ErickHuancas/FdD_Equipo_03/Proyecto/Módulo Mecánico/V3.0/Bocetos/Estructura interna frontal V.3.0.pdf

Título del Proyecto: | Estructura interna frontal del dispositivo

Dibujado por:

Paloma Fernanda
Velasquez Saforas

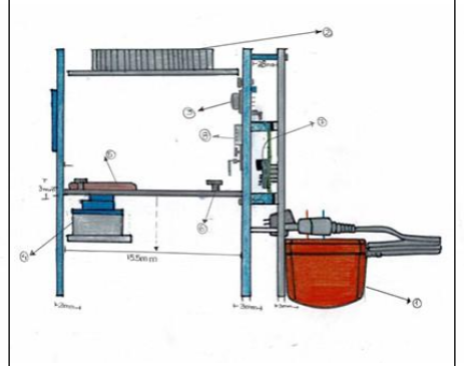
[picture p7: figure]

Descripción del funcionamiento | Lista de Despiece
La vista interna frontal del dispositivo muestra la distribución de los componentes encargados de la captura y procesamiento de datos. En la parte superior se encuentran el módulo ESP32-CAM, la luz LED, el sensor de gas MQ135 y el sensor de temperatura y humedad DHT22, que permiten la adquisición de imágenes y el monitoreo de las condiciones ambientales. En la zona central se ubica | Pieza | Nombre
| 1 | Cargador
| 2 | Luz led
| 3 | Sensor de gas (MQ135)
| 4 | Servomotor
| 5 | Base de soporte del tomate
| 6 | Tornillo

la base de soporte del tomate, acoplada a un servomotor que facilita su rotación para la captura de imágenes desde diferentes ángulos. Finalmente, el sistema es alimentado mediante un cargador y los componentes se encuentran fijados mediante

7 | Módulo ESP32-CAM

t

o

rn

i

l

l

o

s. 8

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
