ErickHuancas/FdD_Equipo_03/Proyecto/Módulo Mecánico/V3.0/Bocetos/Estructura interna V.3.0.pdf

Título del Proyecto: | Estructura externa del dispositivo

Dibujado por:

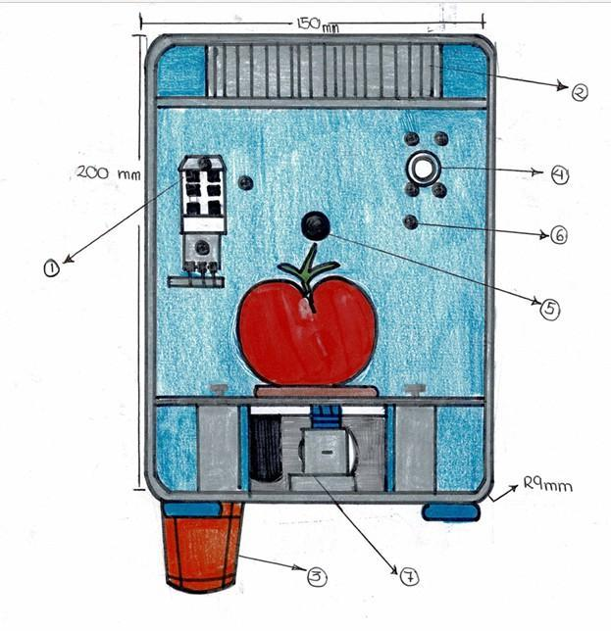
[picture p8: figure]

Paloma Fernanda
Velasquez Saforas
Descripción del funcionamiento | Lista de Despiece
| Pieza | Nombre
| 1 | Sensor de temperatura y humedad (DHT22)
| 2 | Luz led
| 3 | Cargador
| 4 | Sensor de gas (MQ135)
| 5 | Cámara
| 6 | Tornillo

7 | Servomotor
