ErickHuancas/FdD_Equipo_03/Proyecto/Módulo Mecánico/V3.0/Bocetos/Parte trasera V.3.0.pdf

Título del Proyecto: | Parte trasera del dispositivo

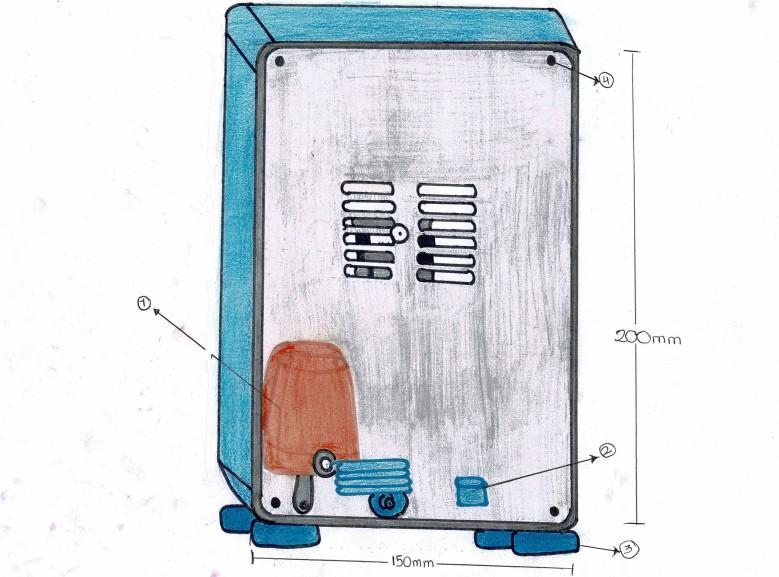
[picture p9: figure]

Dibujado por:

Paloma Fernanda
Velasquez Saforas
Descripción del funcionamiento | Lista de Despiece
| Pieza | Nombre
| 1 | El cargador
| 2 | Interruptor de encendido y apagado
| 3 | soportes
| 4 | tornillos

En la parte tracera del dispositivo se encuentran diversos elementos que facilitan su operación y mantenimiento. El cargador permite suministrar energía eléctrica al sistema para el funcionamiento de los componentes electrónicos. Asimismo, incorpora un interruptor de encendido y apagado, el cual permite controlar el suministro de energía y activar o desactivar el equipo de manera segura.

La estructura también cuenta con soportes ubicados en la base, encargados de proporcionar estabilidad y mantener el dispositivo en una posición adecuada durante su funcionamiento. Además, dispone de tornillos de fijación que aseguran el ensamblaje de la carcasa y permiten el acceso al interior del equipo para labores de mantenimiento o inspección.
