ErickHuancas/FdD_Equipo_03/Proyecto/Módulo Mecánico/Cerfificados/Rose Suazo/CertificadosUnidos.pdf

Onshape Fundamentals

June 21, 2026

Rose Suazo Davila

Rose Suazo Davila

CAD Basics

June 21, 2026

Rose Suazo Davila

Introduction to Sketching

May 01, 2026

Rose Suazo Davila

Introduction to Part Studios

May 01, 2026

Rose Suazo Davila

May 01, 2026

Introduction to Onshape Assemblies

Rose Suazo Davila

May 01, 2026

Detailed Drawings

Rose Suazo Davila

May 21, 2026

Introduction to Drawings

Rose Suazo Davila

Advanced Onshape Assemblies

May 21, 2026
