ErickHuancas/FdD_Equipo_03/Proyecto/Módulo Mecánico/VFINAL/Bocetos/Estructura externa  del dispositivo VFINAL.pdf

Título del Proyecto: | Estructura externa del dispositivo

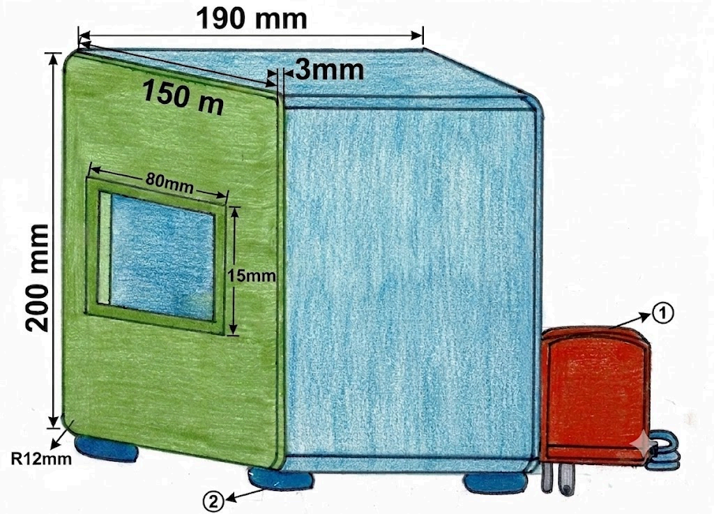
[picture p10: figure]

Dibujado por:

Paloma Fernanda
Velasquez Saforas
Descripción del funcionamiento | Lista de Despiece
| Pieza | Nombre
| 1 | Sensor de temperatura y humedad (DHT22)
| 2 | Luz led
| 3 | Cargador
| 4 | Sensor de gas (MQ135)
| 5 | Cámara
| 6 7 | Tornillo Servomotor

En la parte externa del dispositivo se encuentra el conector de alimentación, encargado de suministrar energía eléctrica al sistema para su correcto funcionamiento. Asimismo, dispone de soportes ubicados en la base, los cuales proporcionan estabilidad y mantienen el equipo en una posición adecuada durante su operación. Además, cuenta con una ventana de inspección que permite observar el interior del dispositivo. Este diseño contribuye a proteger los componentes internos y a mantener condiciones adecuadas para el proceso de evaluación.
