ErickHuancas/FdD_Equipo_03/Proyecto/Módulo Mecánico/VFINAL/Bocetos/Estructura externa del dispositivo VFINAL.pdf

Título del Proyecto: | Estructura externa del dispositivo

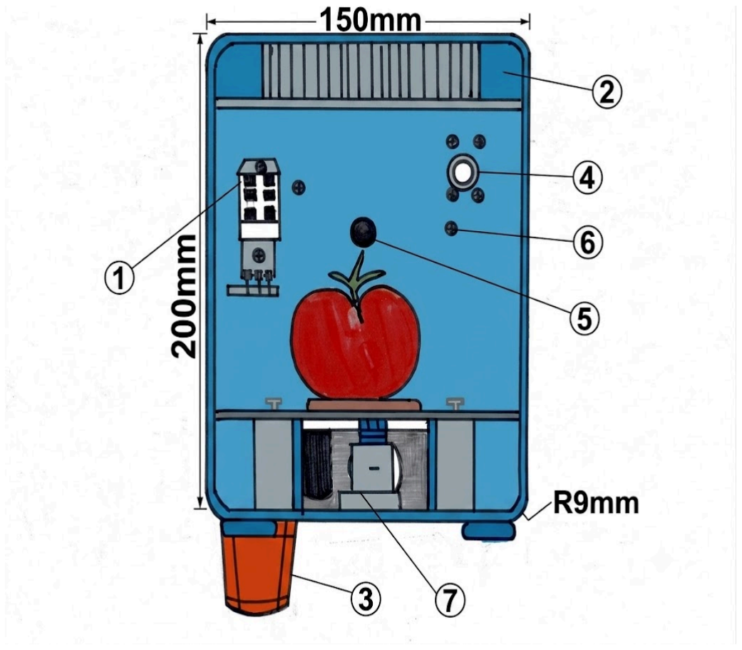
[picture p11: figure]

Dibujado por:

Paloma Fernanda
Velasquez Saforas
Descripción del funcionamiento | Lista de Despiece
| Pieza | Nombre
| 1 | Sensor de temperatura y humedad (DHT22)
| 2 | Luz led
| 3 | Cargador
| 4 | Sensor de gas (MQ135)
| 5 | Cámara
| 6 7 | Tornillo Servomotor

El dispositivo funciona mediante la integración de una cámara, sensores y actuadores que permiten monitorear y evaluar el estado del tomate. La cámara captura imágenes del fruto, mientras que la luz LED proporciona una iluminación adecuada para mejorar la calidad de las imágenes. El sensor DHT22 mide la temperatura y humedad del ambiente, y el sensor de gas MQ135 detecta gases asociados a los procesos de maduración o deterioro. Todos estos datos son utilizados para el análisis del tomate y la estimación de su vida útil. La alimentación del sistema se realiza mediante un cargador, mientras que un servomotor acciona el mecanismo de movimiento interno cuando es necesario. Finalmente, los tornillos aseguran la correcta fijación y estabilidad de los componentes dentro de la estructura del dispositivo.
