ErickHuancas/FdD_Equipo_03/Proyecto/Módulo Mecánico/V1.0/Bocetos/Boceto interior V1.0.pdf

Título del Proyecto: | Dispositivo embebido de estimación de vida útil y clasificación del estado de madurez del tomate mediante sensores ambientales y visión artificial tipo 1
Dibujado por: | Suazo Dávila Rose Angel

BOCETO – Vista 1: Perspectiva interior

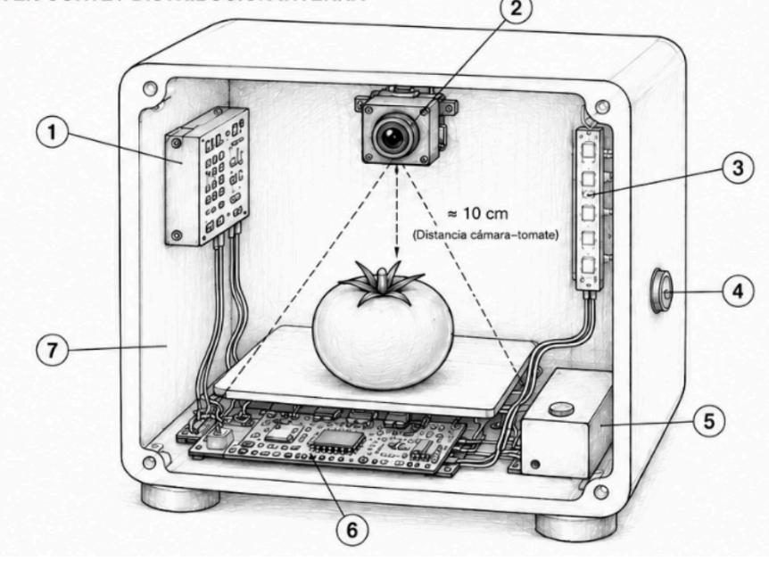
[picture p22: figure]

Descripción del funcionamiento | Lista de Despiece
| Pieza | Nombre
| 1 Sensores (térmico y capacitivo, MOS)
| 2 | Cámara CMOS 2 MP para captura de imágenes del tomate (visión artificial)
| 3 Tira de LED blancos
| 4 Interruptor botón pulsante
| 5 Baterías Li-Ion recargables
| 6 | Bandeja inferior (Componentes electrónicos: Microcontrolador, etc)
| 7 Carcasa -impresión 3D

El dispositivo se alimenta con baterías Li-Ion

reguladas por fuentes conmutadas. Al presionar el

botón pulsador, el microcontrolador se activa y, al

recibir el comando desde el dashboard, la tira LED

ilumina el tomate mientras el sensor CMOS

captura su imagen y los sensores térmico-

capacitivo y MOS miden temperatura, humedad y

gases. El conversor ADC digitaliza las señales y el

modelo Edge Impulse predice el estado de

madurez y vida útil. Los resultados se envían vía

MQTT a la nube y se muestran en el dashboard

para la toma de decisión del operario. La carcasa

es de impresión 3D sellada con juntas de silicona.
