ErickHuancas/FdD_Equipo_03/Proyecto/Módulo Mecánico/V1.0/Bocetos/Boceto isométrico V1.0.pdf

Título del Proyecto: | Dispositivo embebido de estimación de vida útil y clasificación del estado de madurez del tomate mediante sensores ambientales y visión artificial tipo 2
Dibujado por: | Suazo Dávila Rose Angel

BOCETO – Vista 2: Perspectiva isométrica

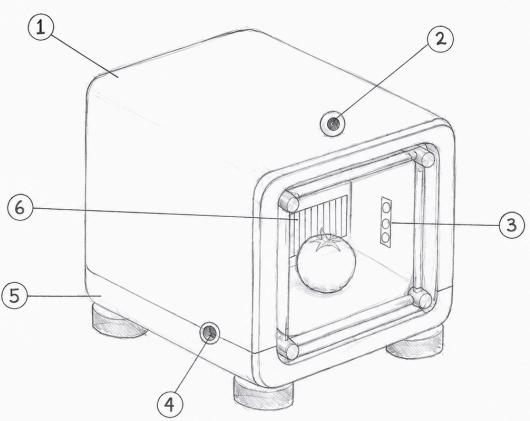
[picture p23: figure]

Descripción del funcionamiento | Lista de Despiece
| Pieza | Nombre
| 1 Carcasa -impresión 3D
| 2 | Cámara CMOS 2 MP para captura de imágenes del tomate (visión artificial)
| 3 Tira de LED blancos
| 4 Interruptor botón pulsante
| 5 | Bandeja inferior (Componentes electrónicos: Microcontrolador, etc)
| 6 Sensores (térmico y capacitivo, MOS)

El dispositivo se alimenta con baterías Li-Ion

reguladas en la bandeja inferior. Al presionar el

pulsador, el microcontrolador se activa; tras recibir

la orden del dashboard, la iluminación LED se

enciende de forma homogénea y la cámara CMOS

captura la imagen del tomate para el análisis de

visión artificial. En paralelo, el módulo de sensores

mide | la | temperatura, | humedad | y | gases

ambientales. Un conversor ADC digitaliza las

señales y el microcontrolador, mediante un modelo

de Edge Impulse, procesa los datos combinados

para clasificar la madurez y estimar la vida útil del

fruto. Los resultados se envían por MQTT a la nube

para su visualización en tiempo real.
