ErickHuancas/FdD_Equipo_03/Proyecto/Módulo Mecánico/V2.0/Bocetos/Boceto lateral V2.0.pdf

Título del Proyecto: | Dispositivo embebido de estimación de vida útil y clasificación del
| estado de madurez del tomate mediante sensores ambientales y visión
| artificial

Dibujado por:

Paloma Fernanda
Velasquez Saforas

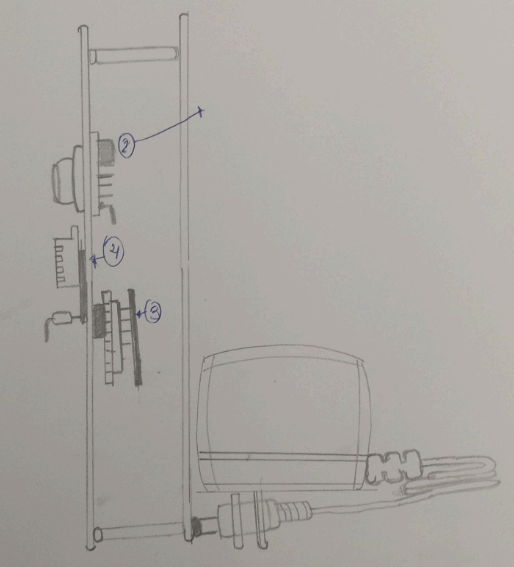
[picture p27: figure]

Descripción del funcionamiento | Lista de Despiece
| Pieza | Nombre
| 1 | Luz led
| 2 | Sensor de gas (MQ135)
| 3 | Cámara
| 4 | Sensor de temperatura y humedad (DHT22)
| 5 | Servomotor

El sistema está diseñado para monitorear las condiciones ambientales y responder automáticamente ante la detección de gases o cambios en el entorno. El sensor MQ135 mide la concentración de gases presentes en el aire, mientras que el sensor DHT22 registra la temperatura y la humedad del ambiente. Además, una cámara permite la captura y supervisión visual del área monitoreada.

Cuando el sensor MQ135 detecta una concentración de gases superior al valor establecido, el sistema activa una luz LED como señal de advertencia. Simultáneamente, el servomotor puede ejecutar una acción mecánica, como abrir una compuerta, una ventana o mover un mecanismo de ventilación para reducir la acumulación de gases.

La información obtenida por los sensores puede ser procesada por un microcontrolador, permitiendo el monitoreo continuo del ambiente y la activación automática de los dispositivos de respuesta. De esta manera, el sistema contribuye a mejorar la seguridad y el control de las condiciones ambientales en el área supervisada.
