ErickHuancas/FdD_Equipo_03/Proyecto/Módulo Software/EdgeImpulse/impulse_arduino.png

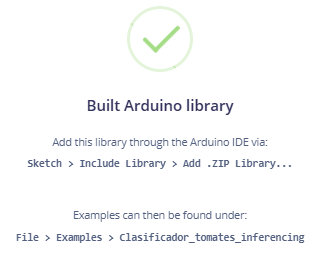
Proyecto/Módulo Software/EdgeImpulse/impulse_arduino.png
