ErickHuancas/FdD_Equipo_03/Proyecto/Módulo Software/EdgeImpulse/impulse_conf.png

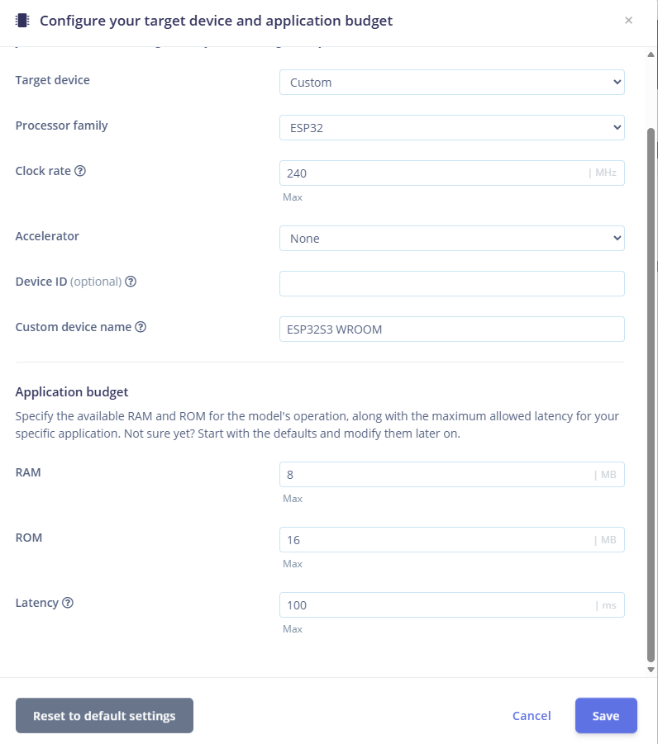
Proyecto/Módulo Software/EdgeImpulse/impulse_conf.png
