ErickHuancas/FdD_Equipo_03/Proyecto/Módulo Software/EdgeImpulse/impulse_deploy.png

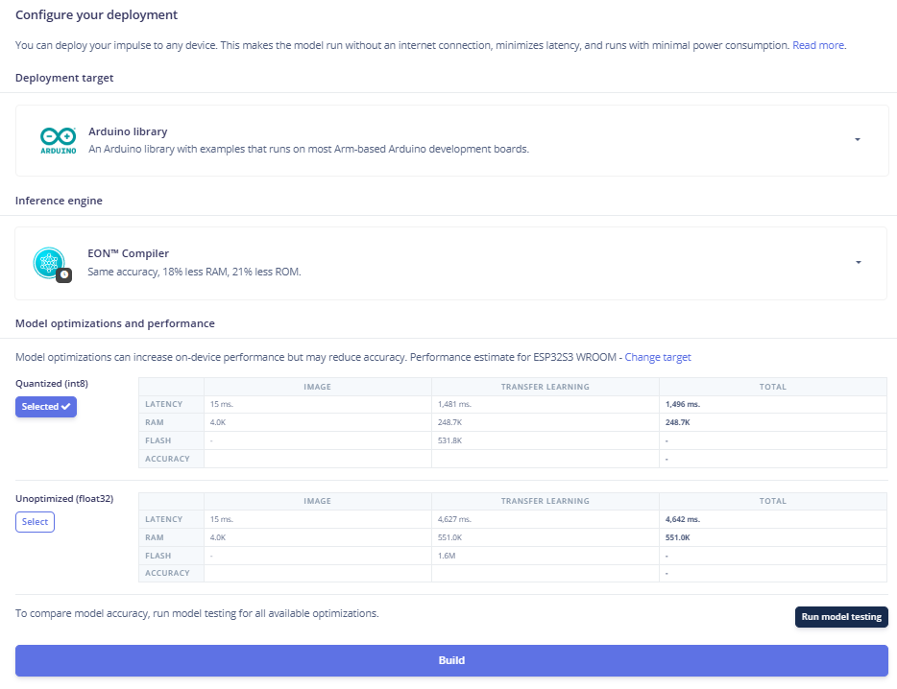
Proyecto/Módulo Software/EdgeImpulse/impulse_deploy.png
