ErickHuancas/FdD_Equipo_03/Proyecto/Módulo Software/EdgeImpulse/impulse_model.png

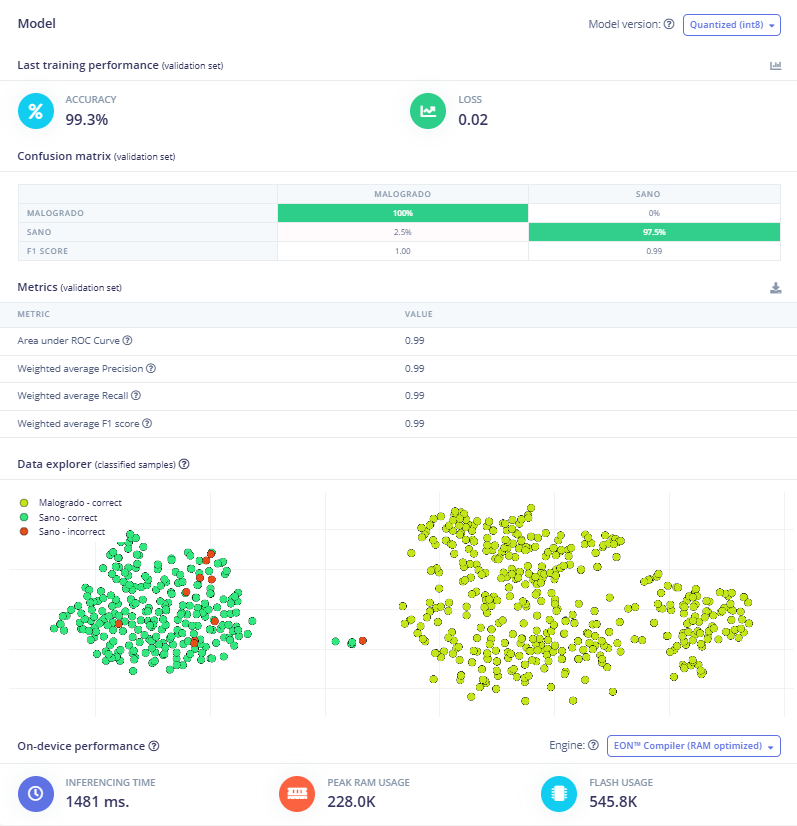
Proyecto/Módulo Software/EdgeImpulse/impulse_model.png
