ErickHuancas/FdD_Equipo_03/Proyecto/Módulo Software/EdgeImpulse/impulse_reconocer.png

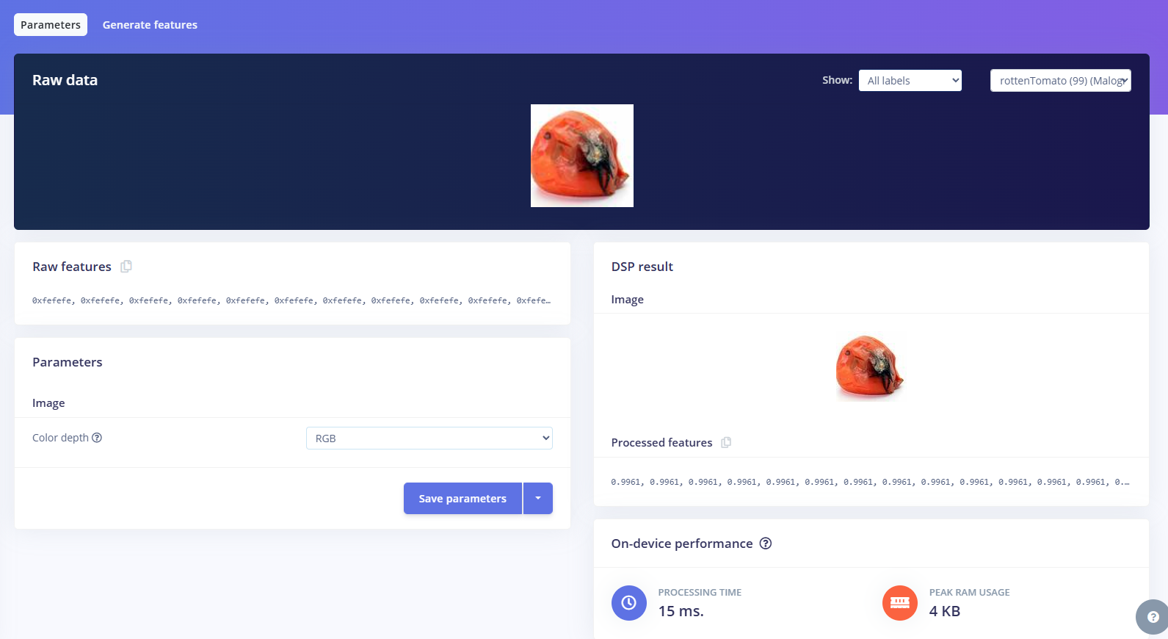
Proyecto/Módulo Software/EdgeImpulse/impulse_reconocer.png
