ErickHuancas/FdD_Equipo_03/Proyecto/Módulo Software/EdgeImpulse/impulse_stage.png

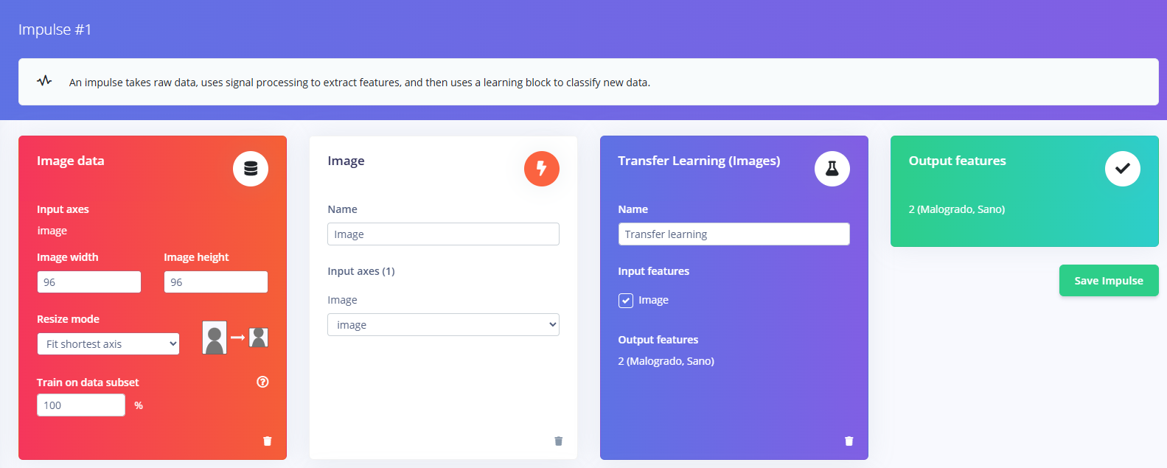
Proyecto/Módulo Software/EdgeImpulse/impulse_stage.png
