ErickHuancas/FdD_Equipo_03/Proyecto/Módulo Software/EdgeImpulse/impulse_transferencia.png

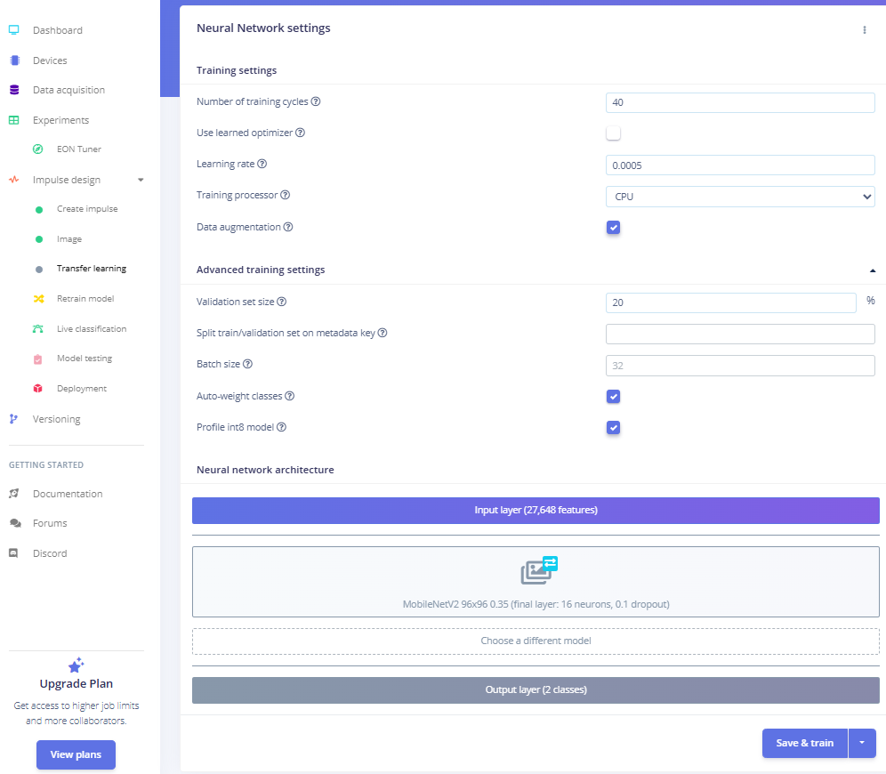
Proyecto/Módulo Software/EdgeImpulse/impulse_transferencia.png
