ErickHuancas/FdD_Equipo_03/Proyecto/Módulo Software/Imagenes de la Interfaz/Imagen3.png

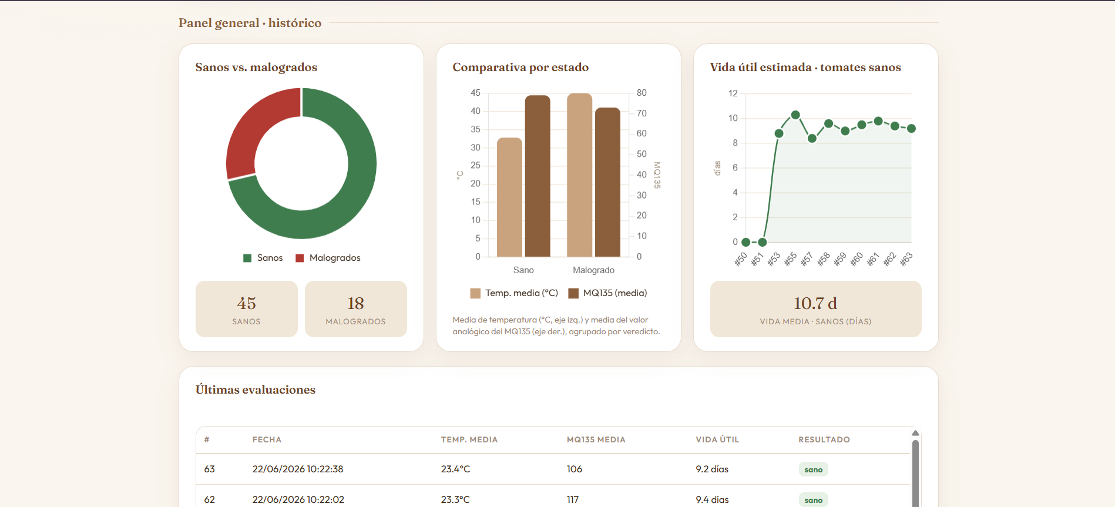
Proyecto/Módulo Software/Imagenes de la Interfaz/Imagen3.png
