ErickHuancas/FdD_Equipo_03/Recursos/Imágenes/Patente5.png

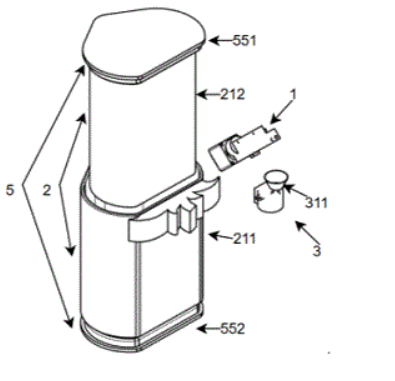
Recursos/Imágenes/Patente5.png
