ErickHuancas/FdD_Equipo_03/Proyecto/Módulo Electrónico/VFINAL/Esquemático VFINAL.pdf

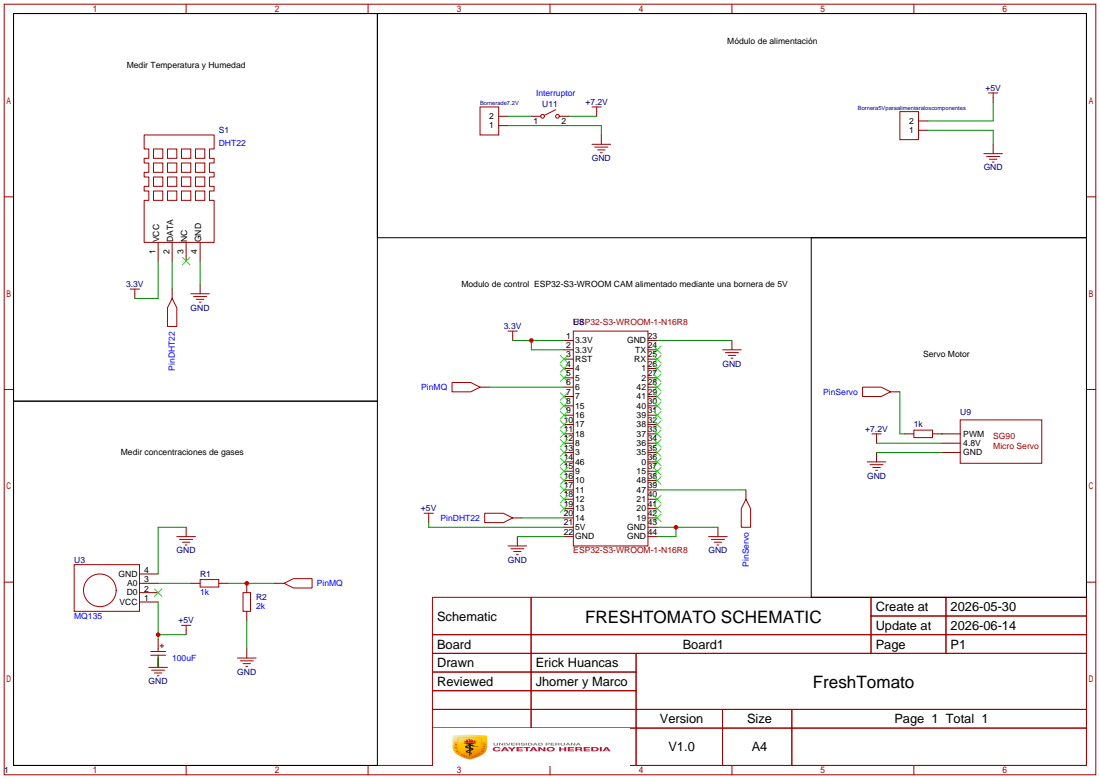
[picture p53: page 1]

Modulo de control ESP32-S3-WROOM CAM alimentado mediante una bornera de 5V

Medir concentraciones de gases

Schematic | FRESHTOMATO SCHEMATIC | Create at | 2026-05-30

Update at | 2026-06-14

Board | Board1 | Page | P1
Drawn | Erick Huancas | FreshTomato
Reviewed | Jhomer y Marco

Version | Size | Page 1 Total 1
V1.0 | A4
