ErickHuancas/FdD_Equipo_03/Proyecto/Módulo Mecánico/V3.0/Onshape/Planos/Base de los sensores V3.0.pdf

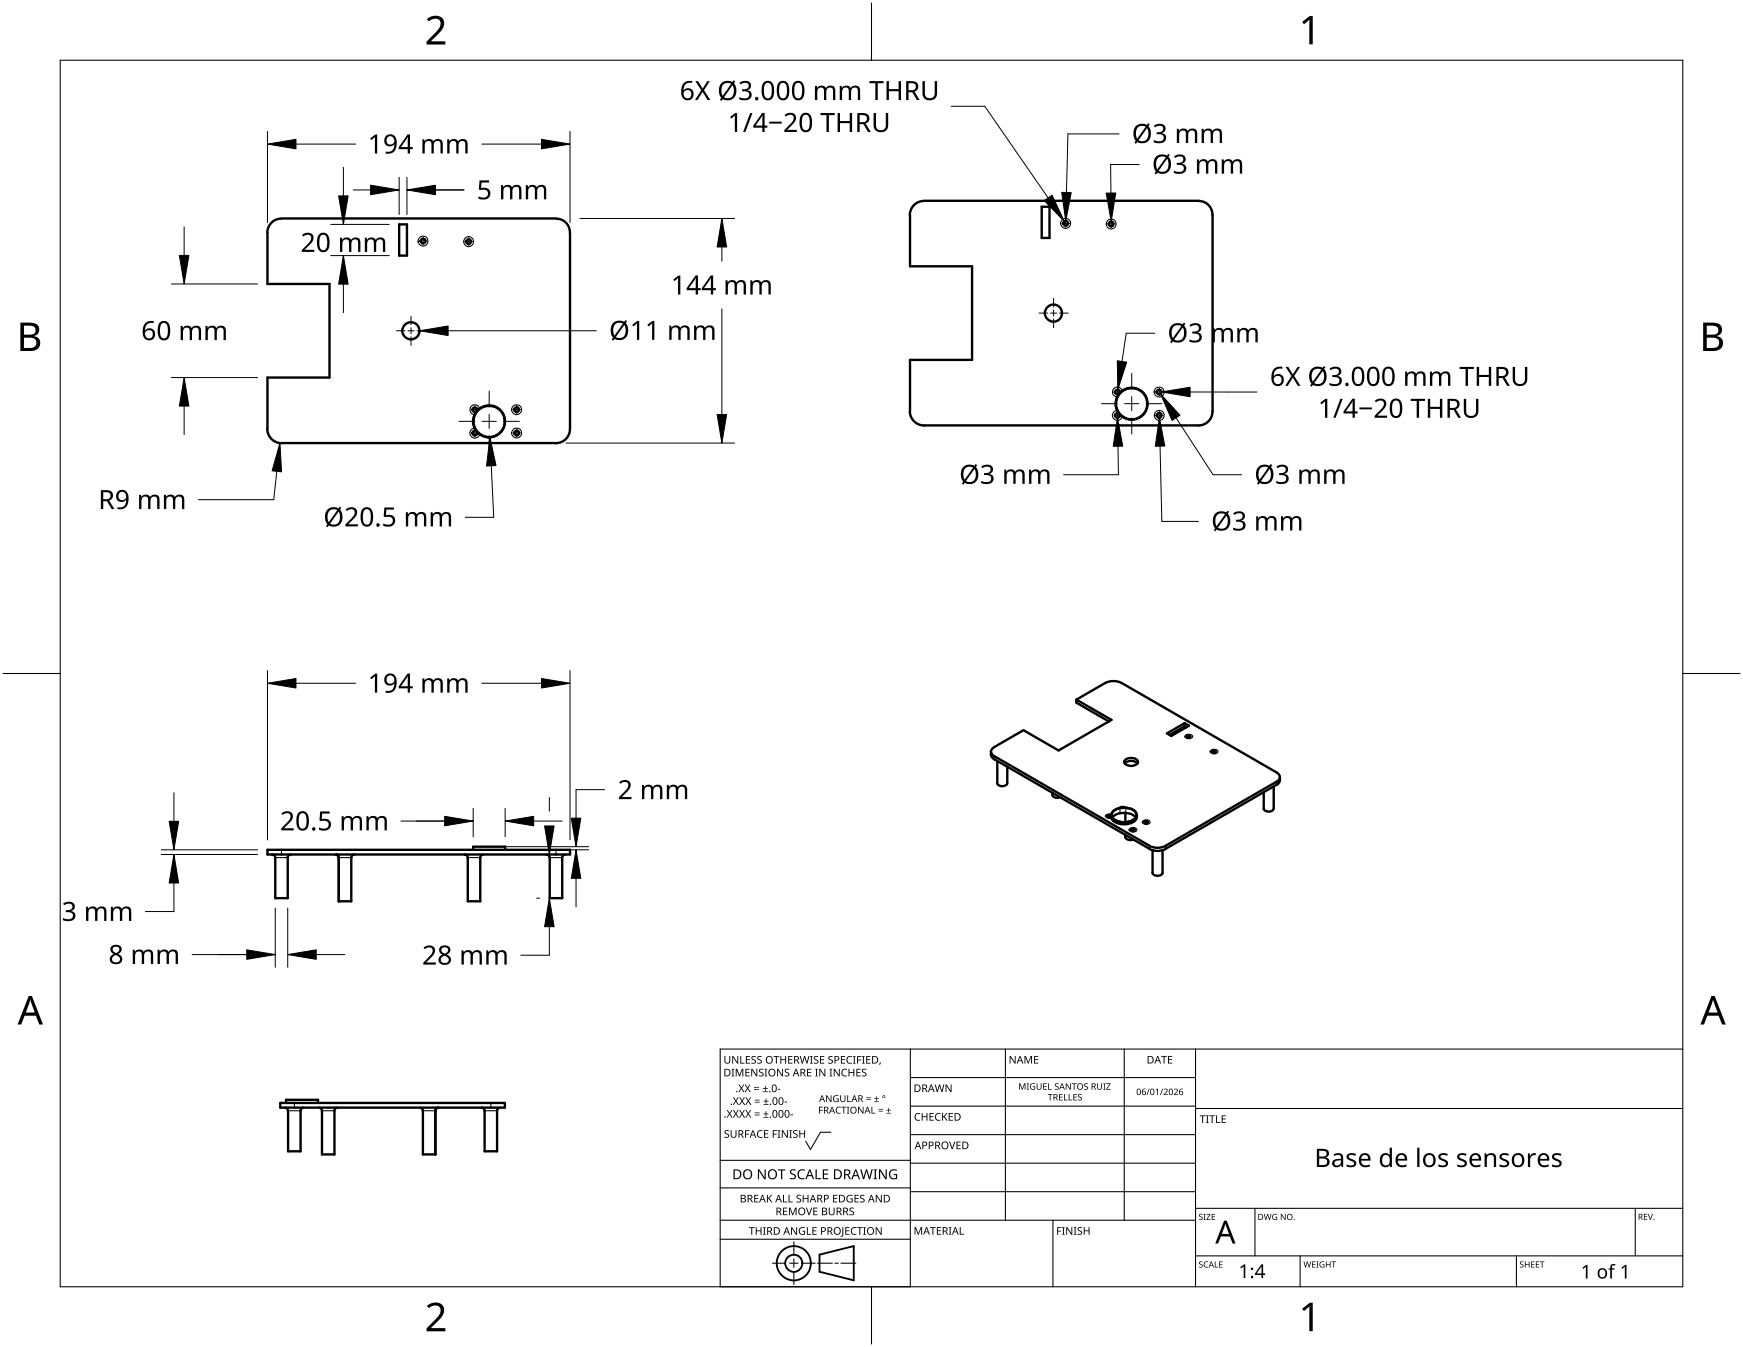
[picture p54: page 1]
