ErickHuancas/FdD_Equipo_03/Proyecto/Módulo Mecánico/V3.0/Onshape/Planos/Base para tomate, unido al servomotor V3.0.pdf

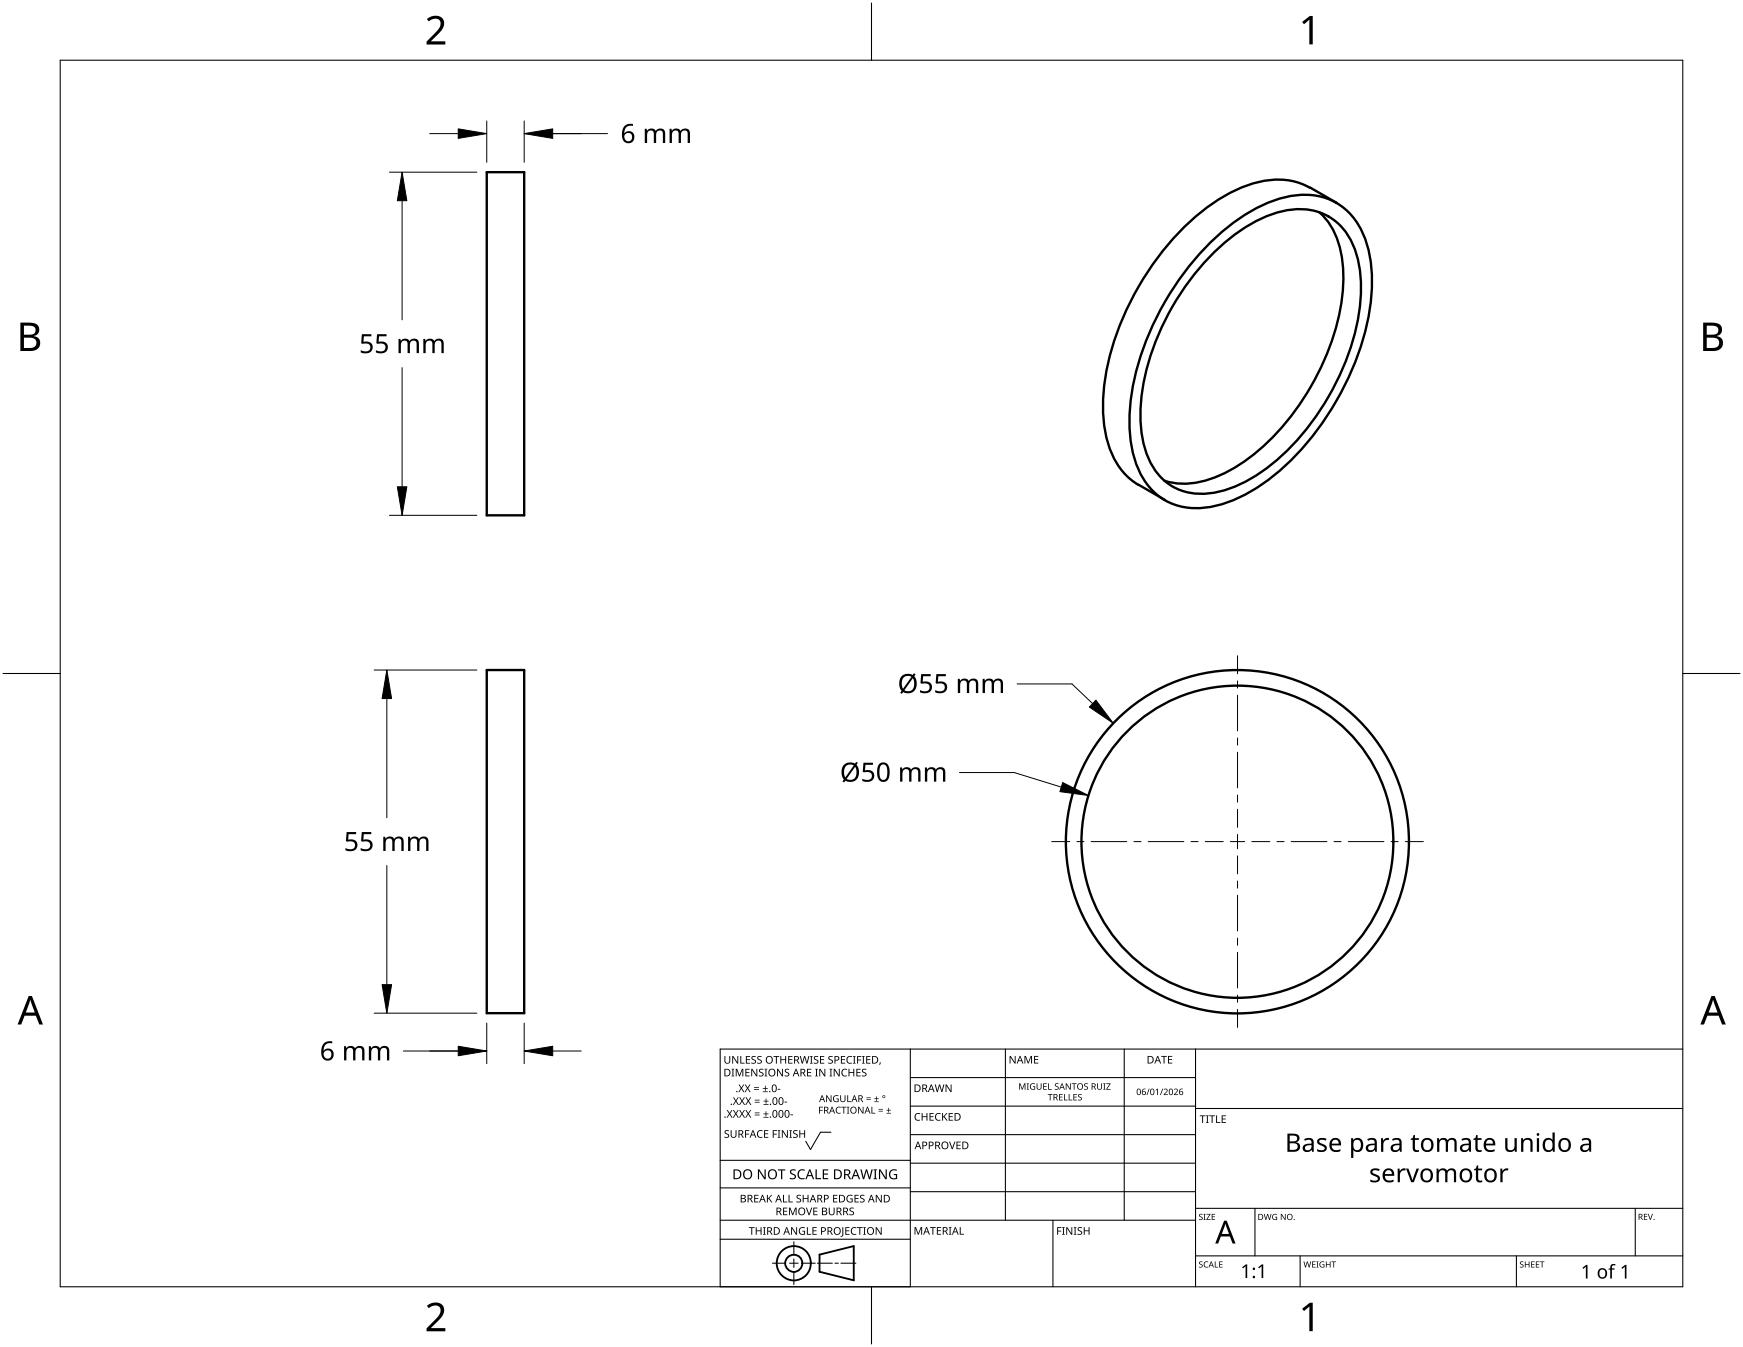
[picture p55: page 1]
