ErickHuancas/FdD_Equipo_03/Proyecto/Módulo Mecánico/V3.0/Onshape/Planos/CAJA DEL PROTOTIPO V3.0.pdf

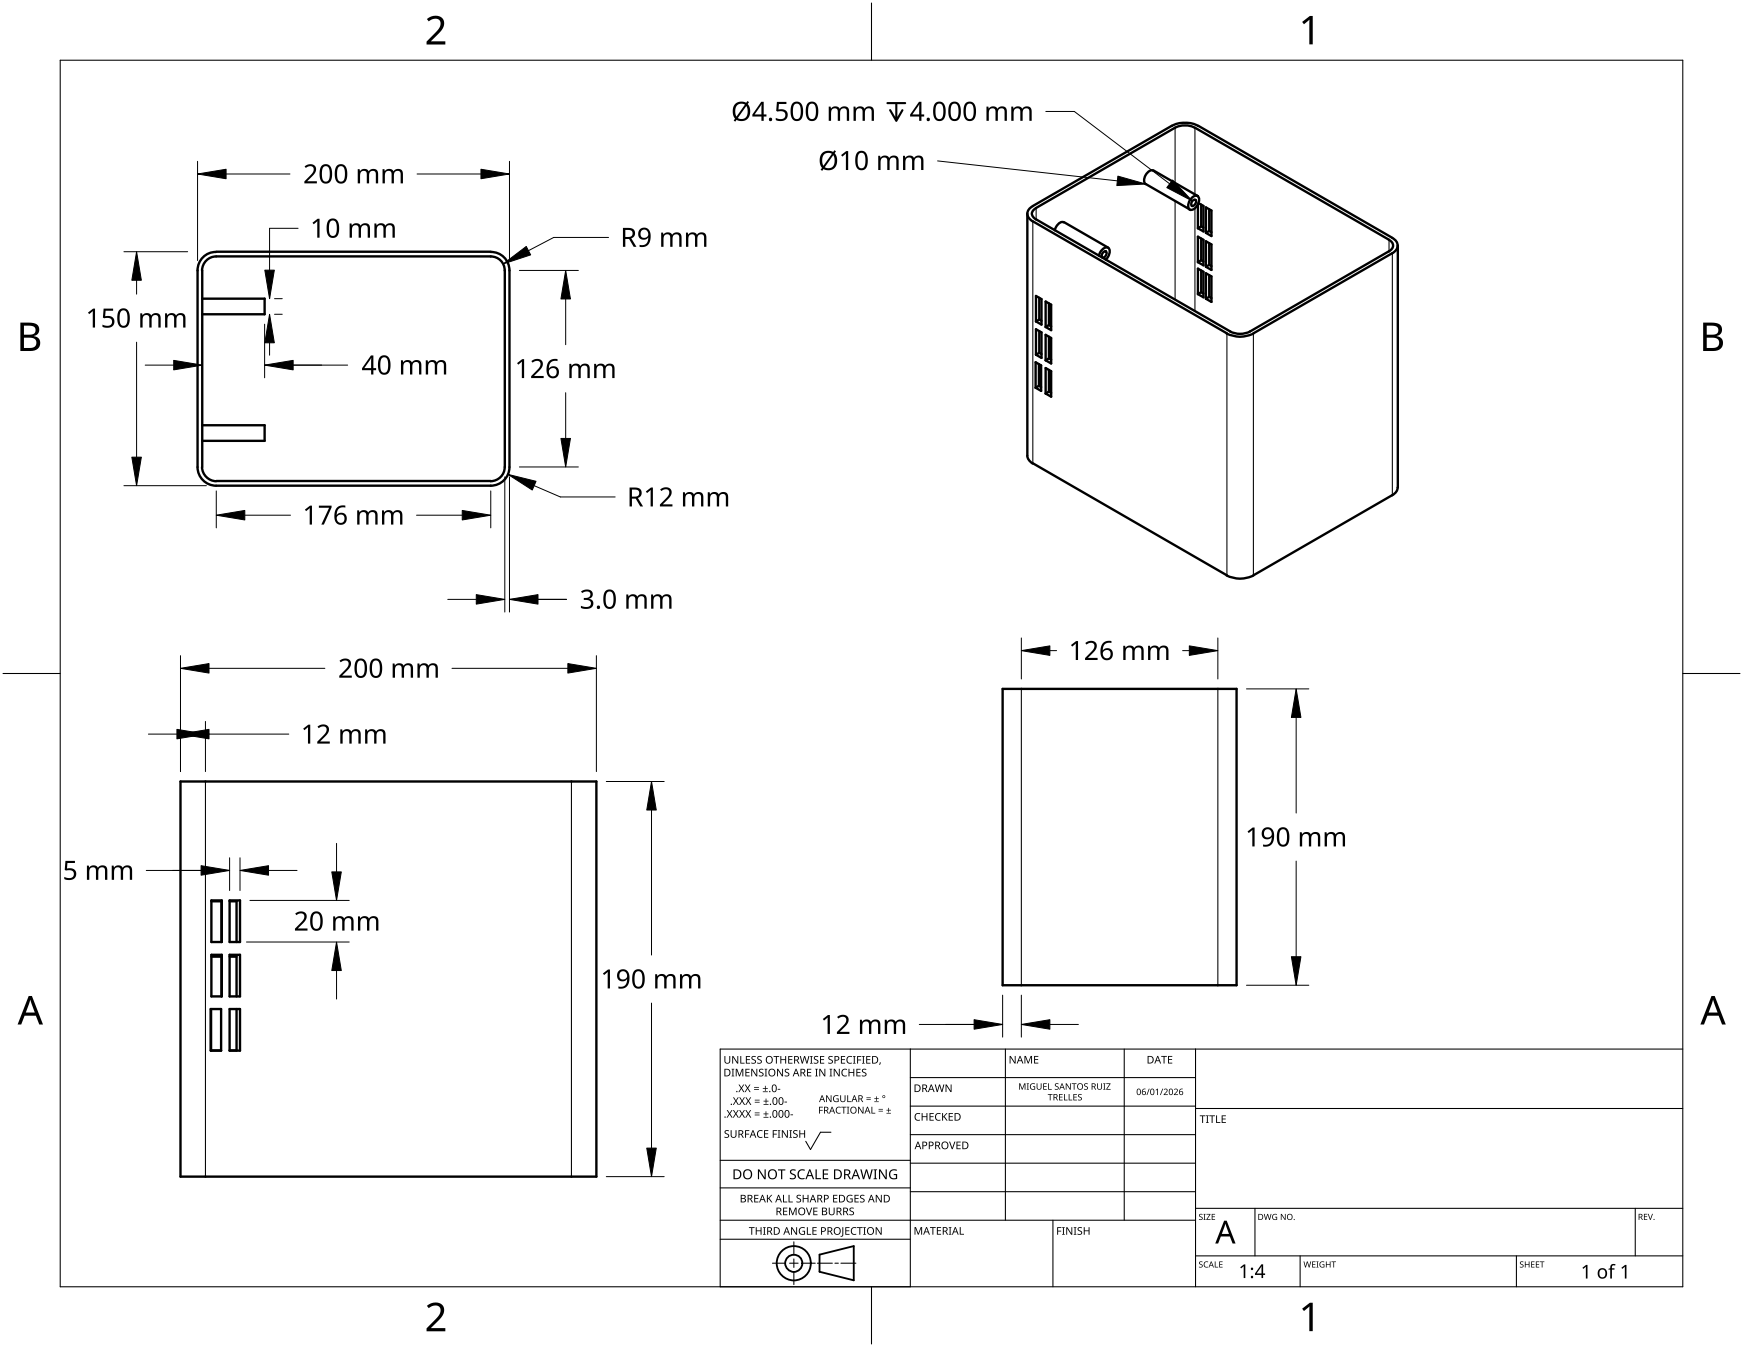
[picture p56: page 1]
