ErickHuancas/FdD_Equipo_03/Proyecto/Módulo Mecánico/V3.0/Onshape/Planos/plataforma de giro del tomate V3.0.pdf

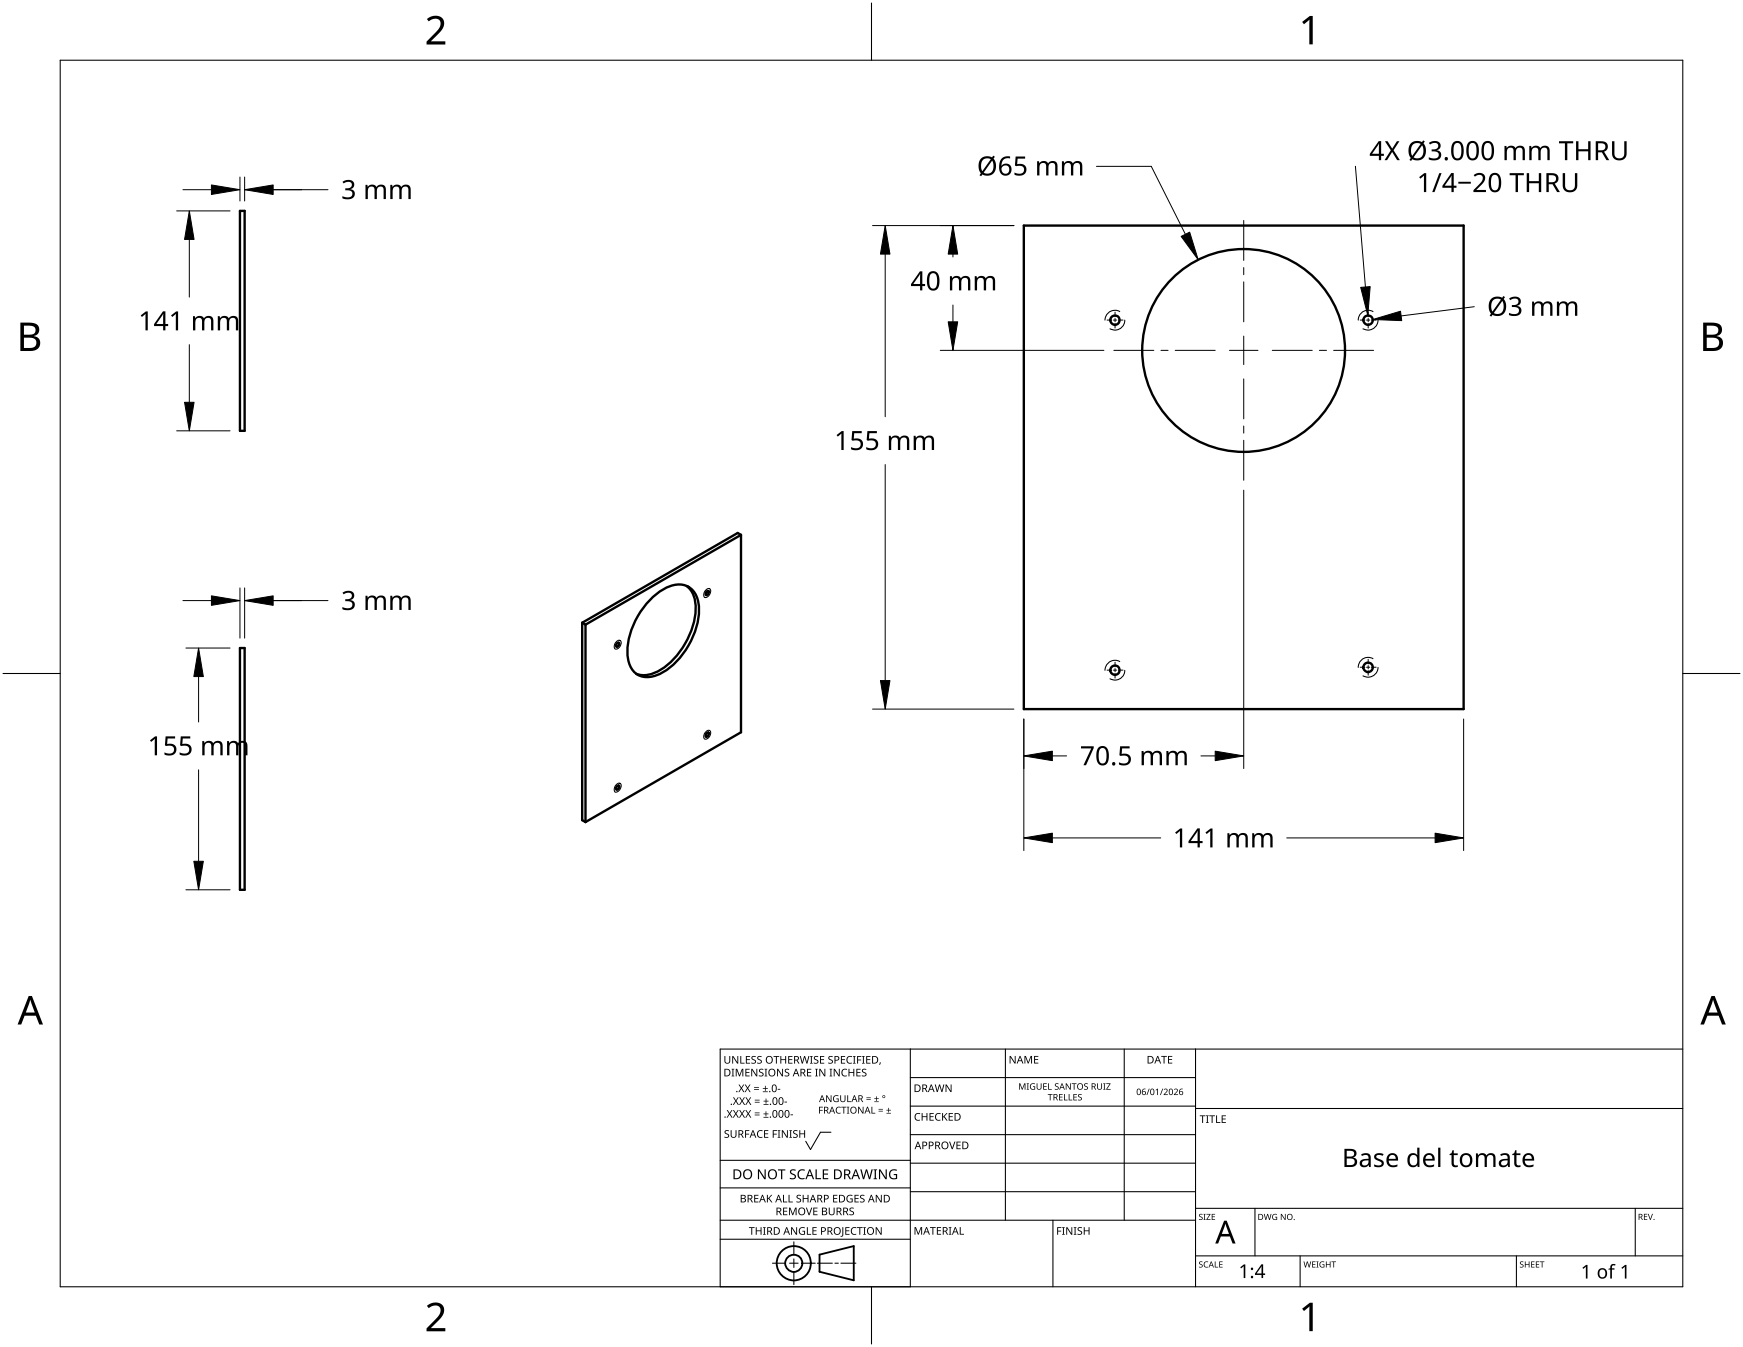
[picture p57: page 1]
