ErickHuancas/FdD_Equipo_03/Proyecto/Módulo Mecánico/V3.0/Onshape/Planos/Soporte de la caja V3.0.pdf

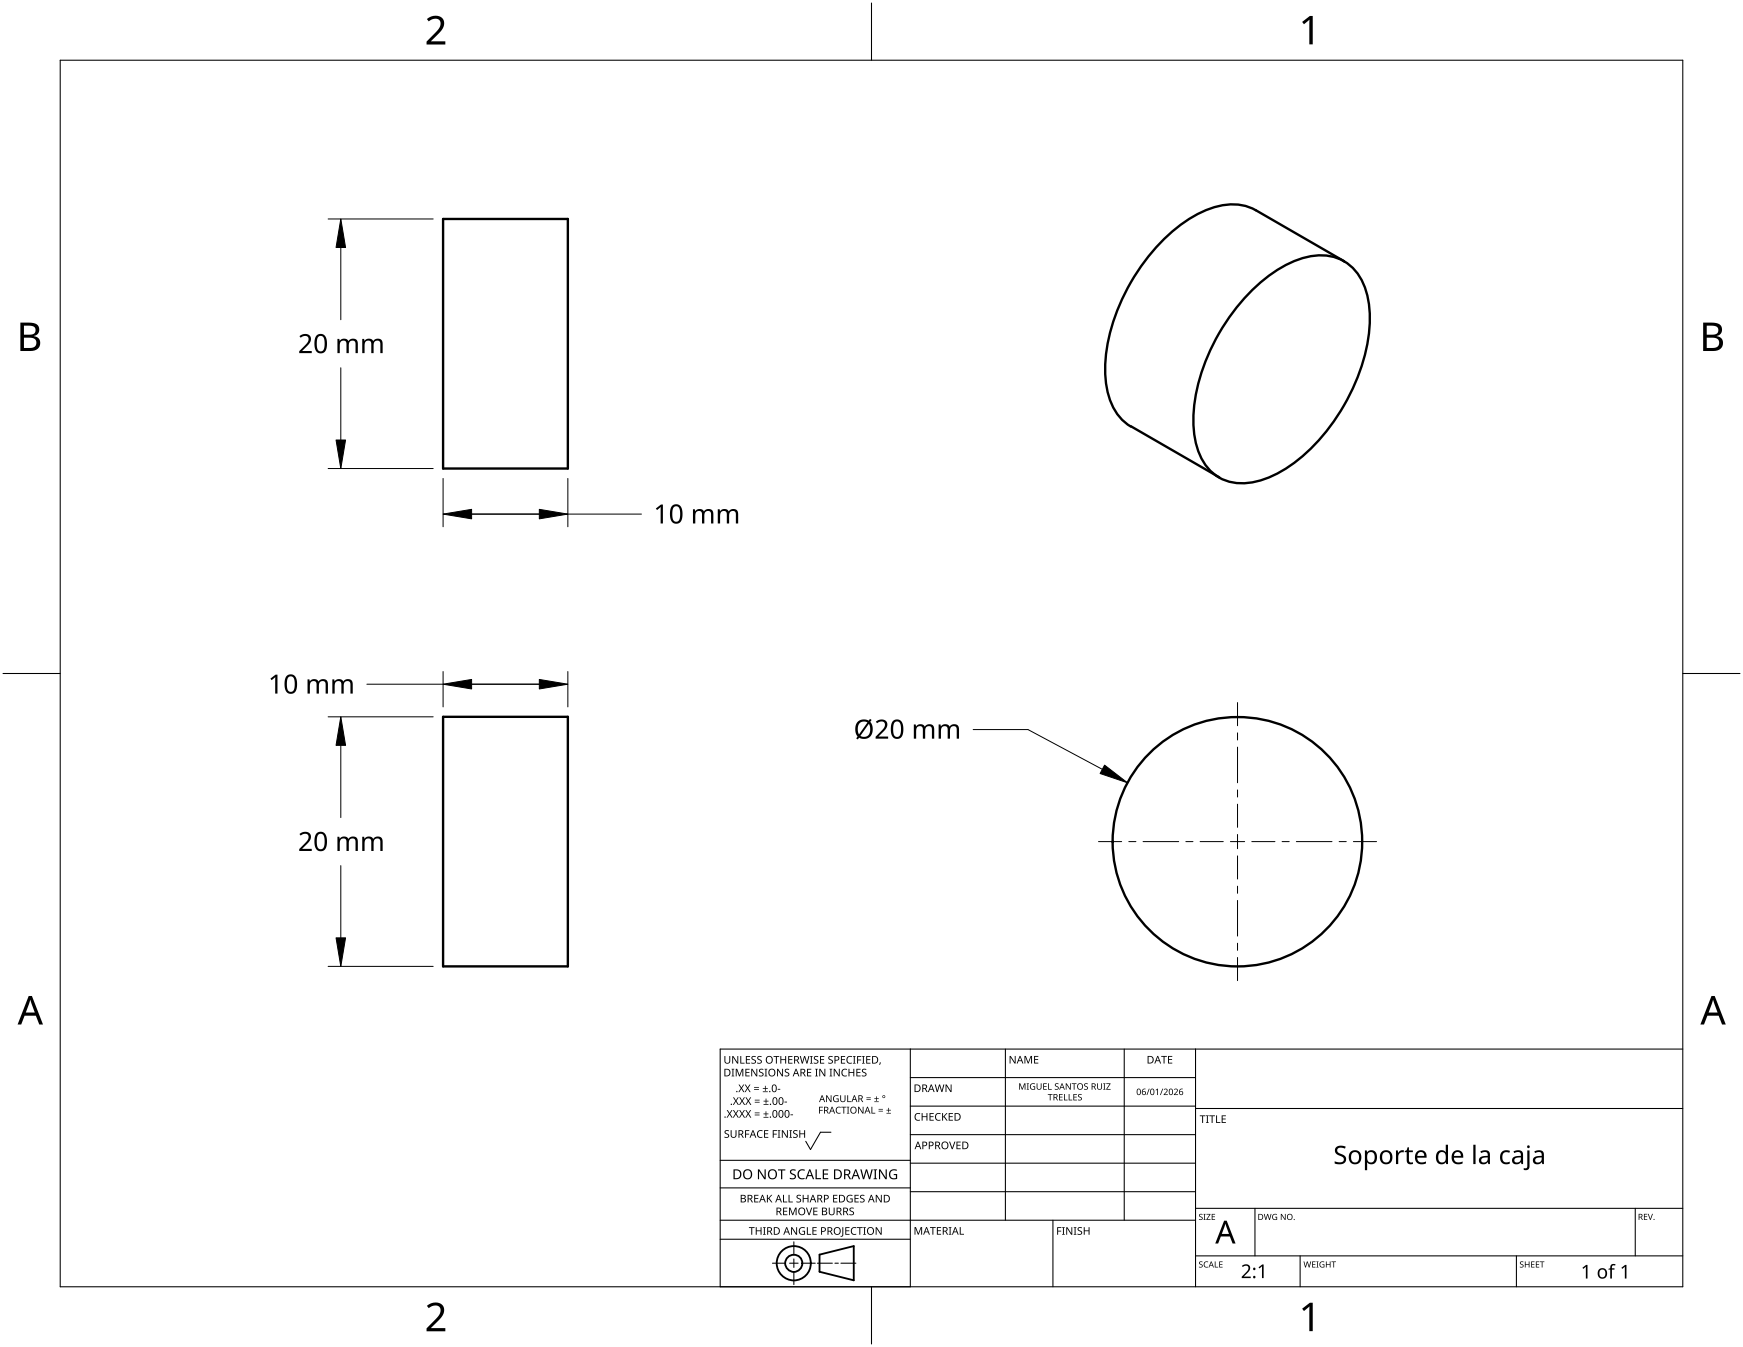
[picture p58: page 1]
