ErickHuancas/FdD_Equipo_03/Proyecto/Módulo Mecánico/V3.0/Onshape/Planos/SOPORTE SERVO V3.0.pdf

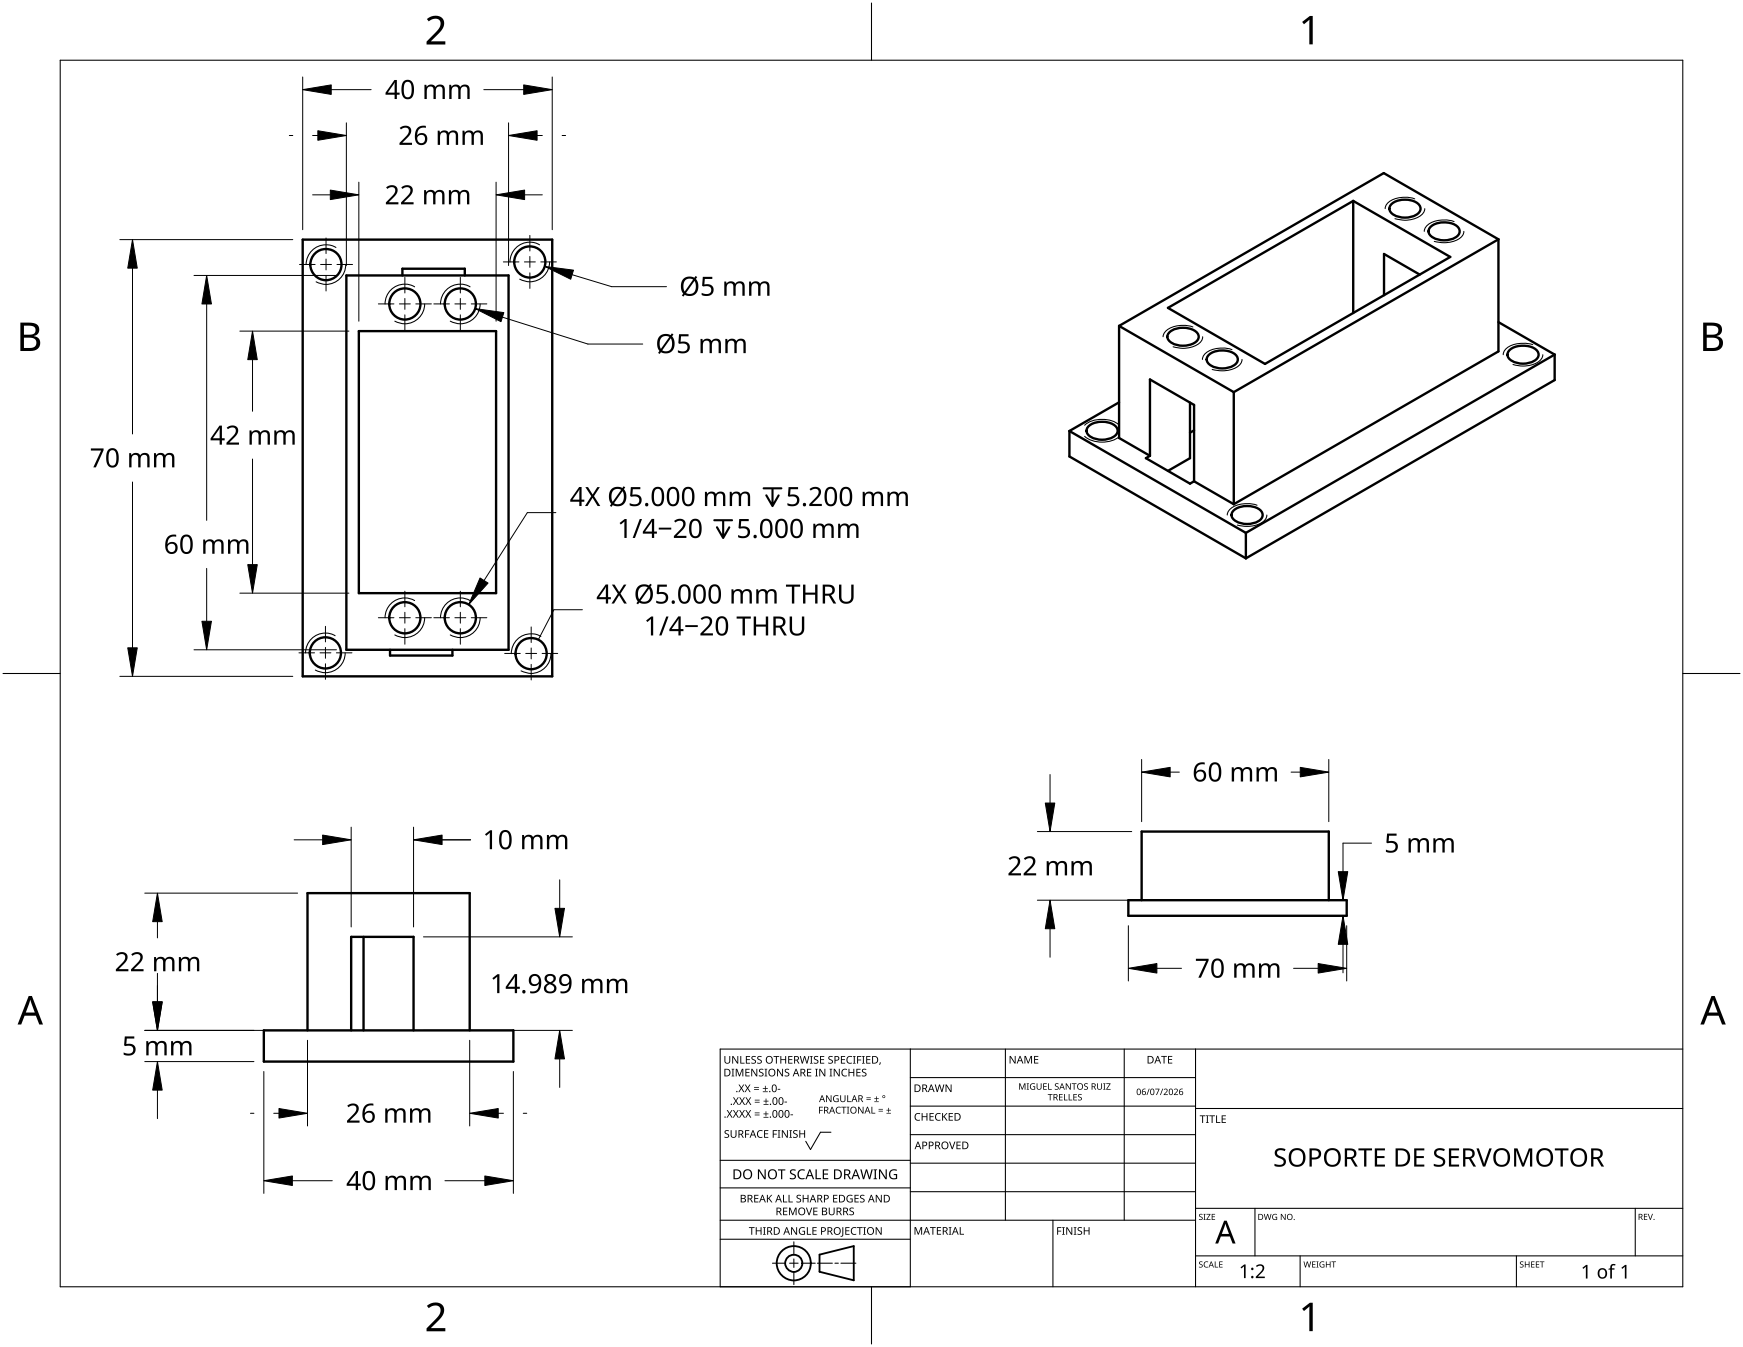
[picture p59: page 1]
