ErickHuancas/FdD_Equipo_03/Proyecto/Módulo Mecánico/V3.0/Onshape/Planos/Tapa delantera V3.0.pdf

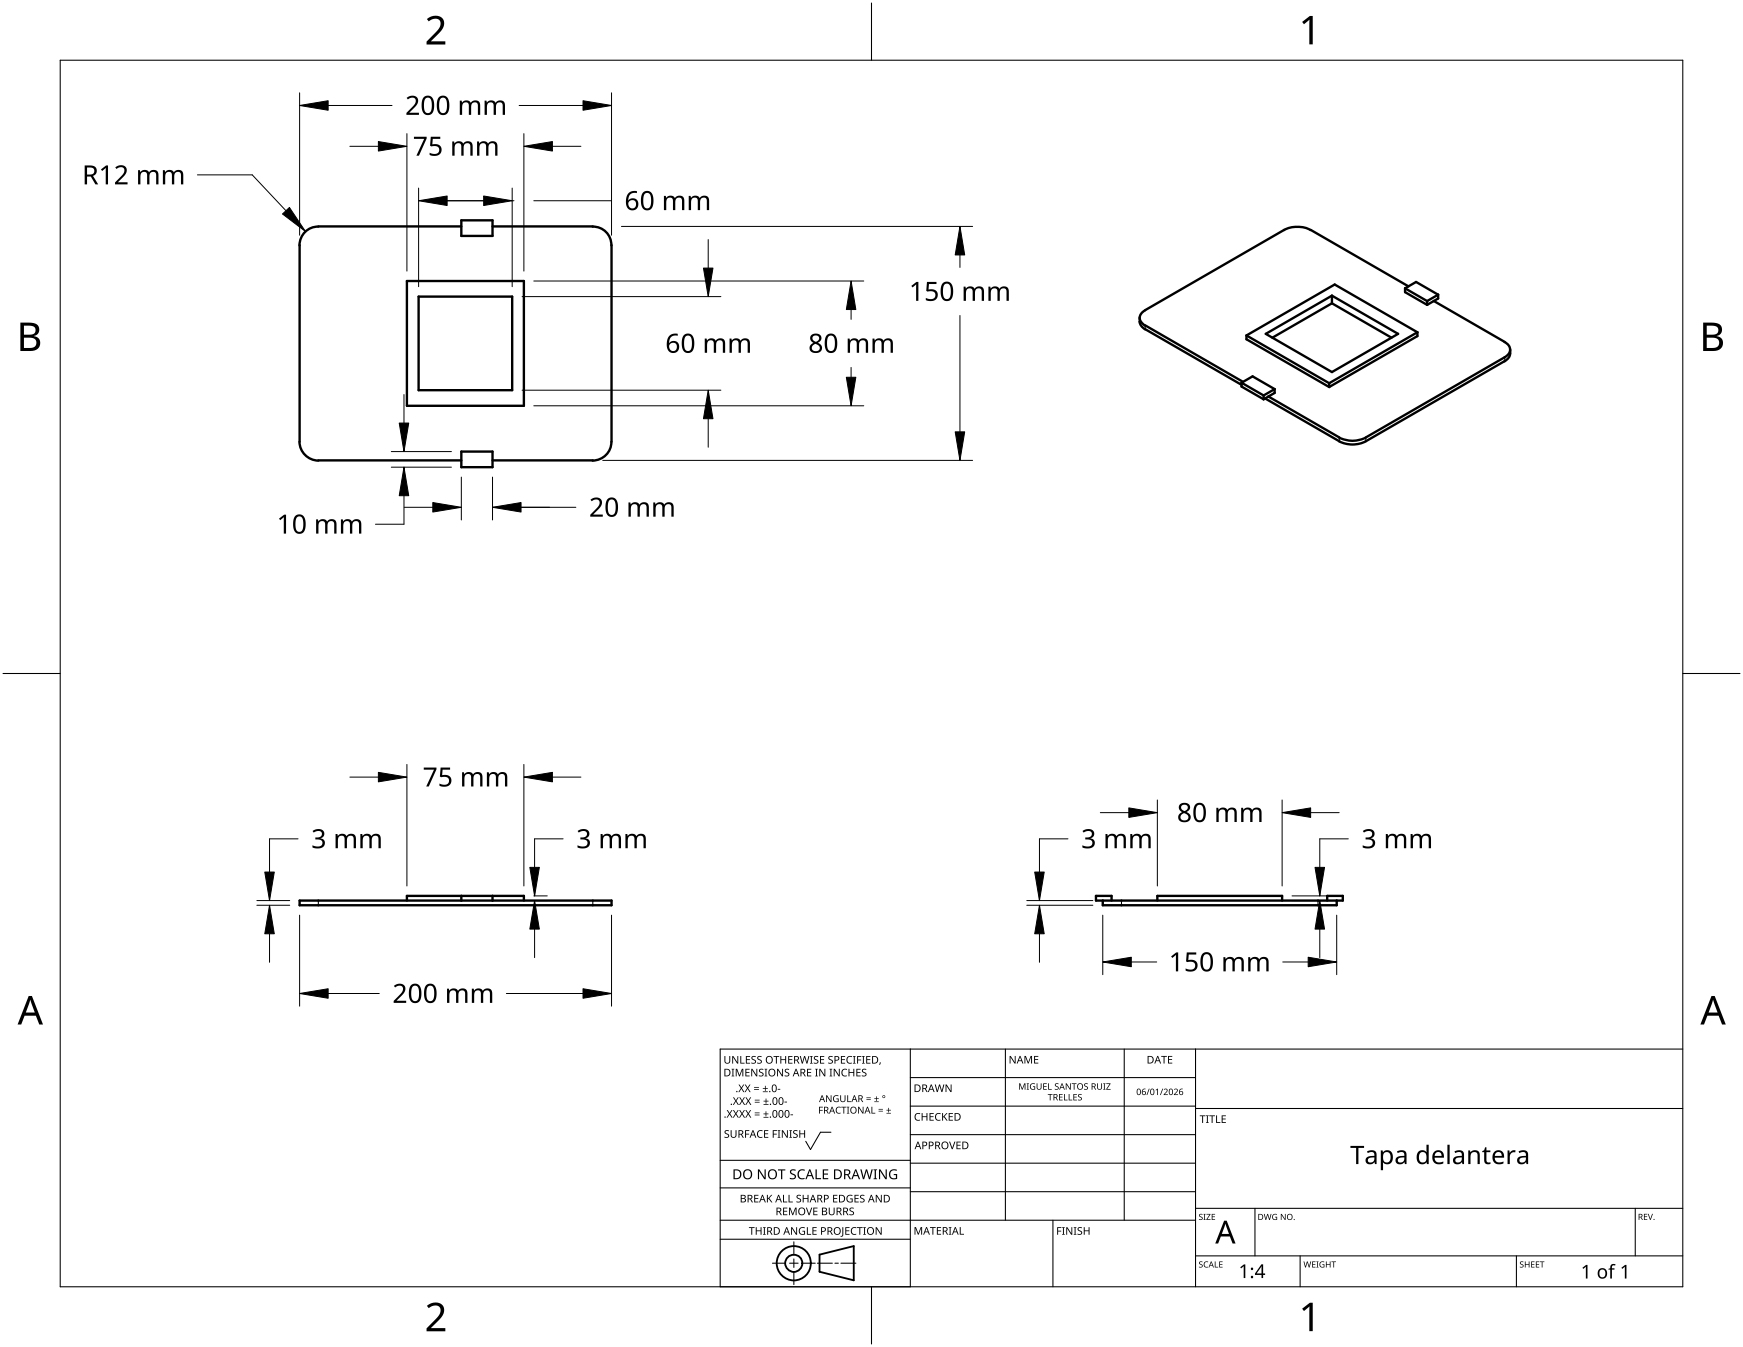
[picture p60: page 1]
