ErickHuancas/FdD_Equipo_03/Proyecto/Módulo Mecánico/V3.0/Onshape/Planos/Tapa trasera V3.0.pdf

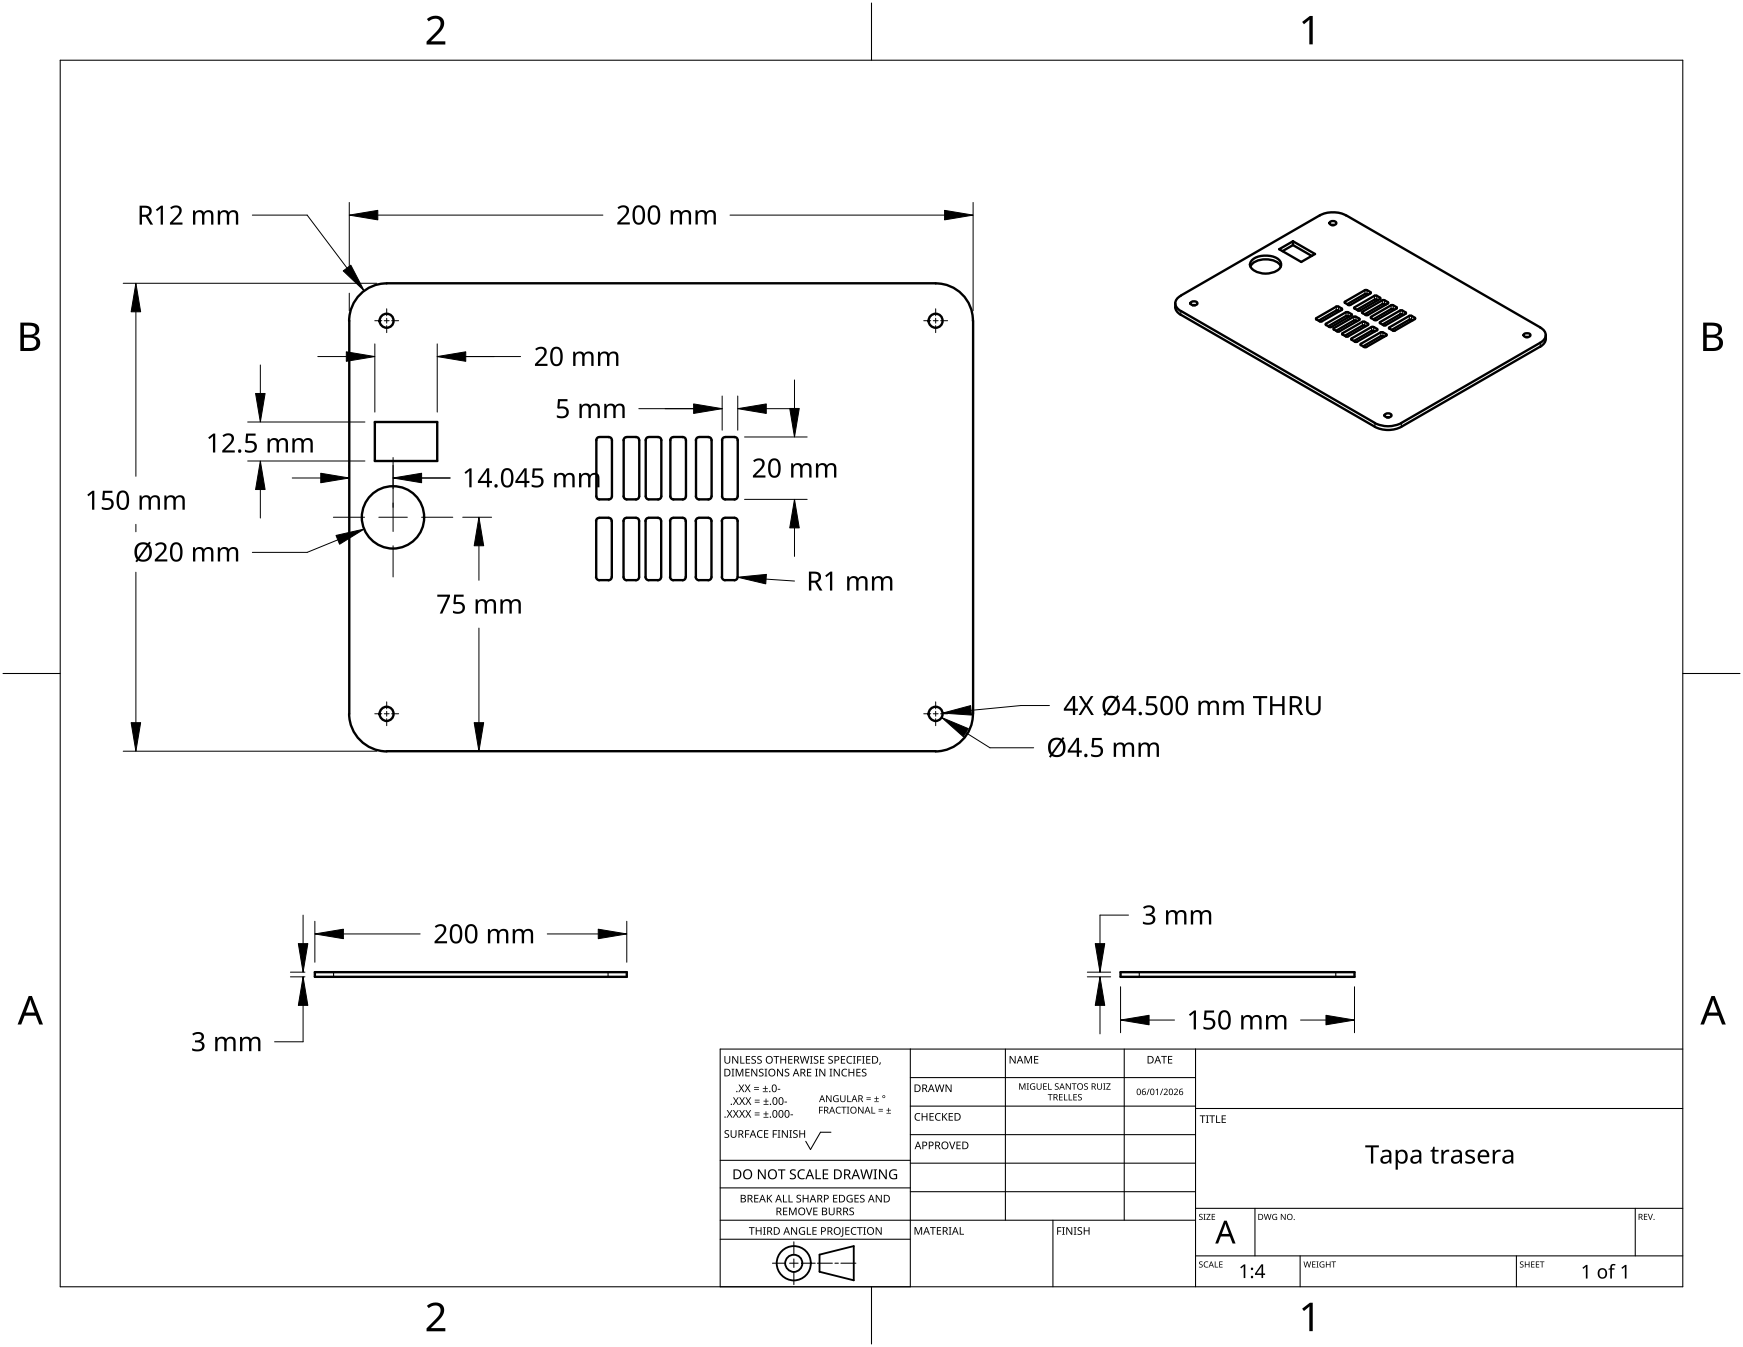
[picture p61: page 1]
