ErickHuancas/FdD_Equipo_03/Proyecto/Módulo Electrónico/V1.0/Esquemático V1.0.pdf

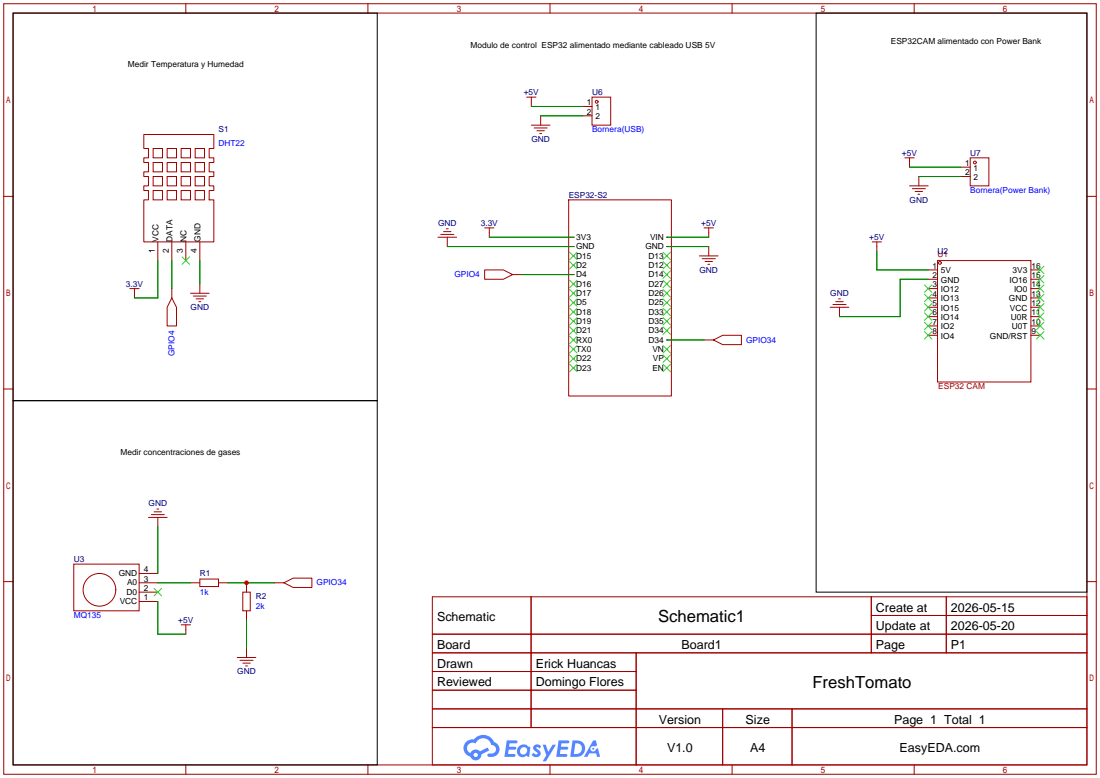
[picture p62: page 1]

Medir concentraciones de gases

Schematic | Schematic1 | Create at | 2026-05-15

Update at | 2026-05-20

Board | Board1 | Page | P1
Drawn | Erick Huancas | FreshTomato
Reviewed | Domingo Flores

Version | Size | Page 1 Total 1
V1.0 | A4 | EasyEDA.com
