ErickHuancas/FdD_Equipo_03/Proyecto/Módulo Mecánico/V2.0/Onshape/Planos/Base circular de movimiento V2.0.pdf

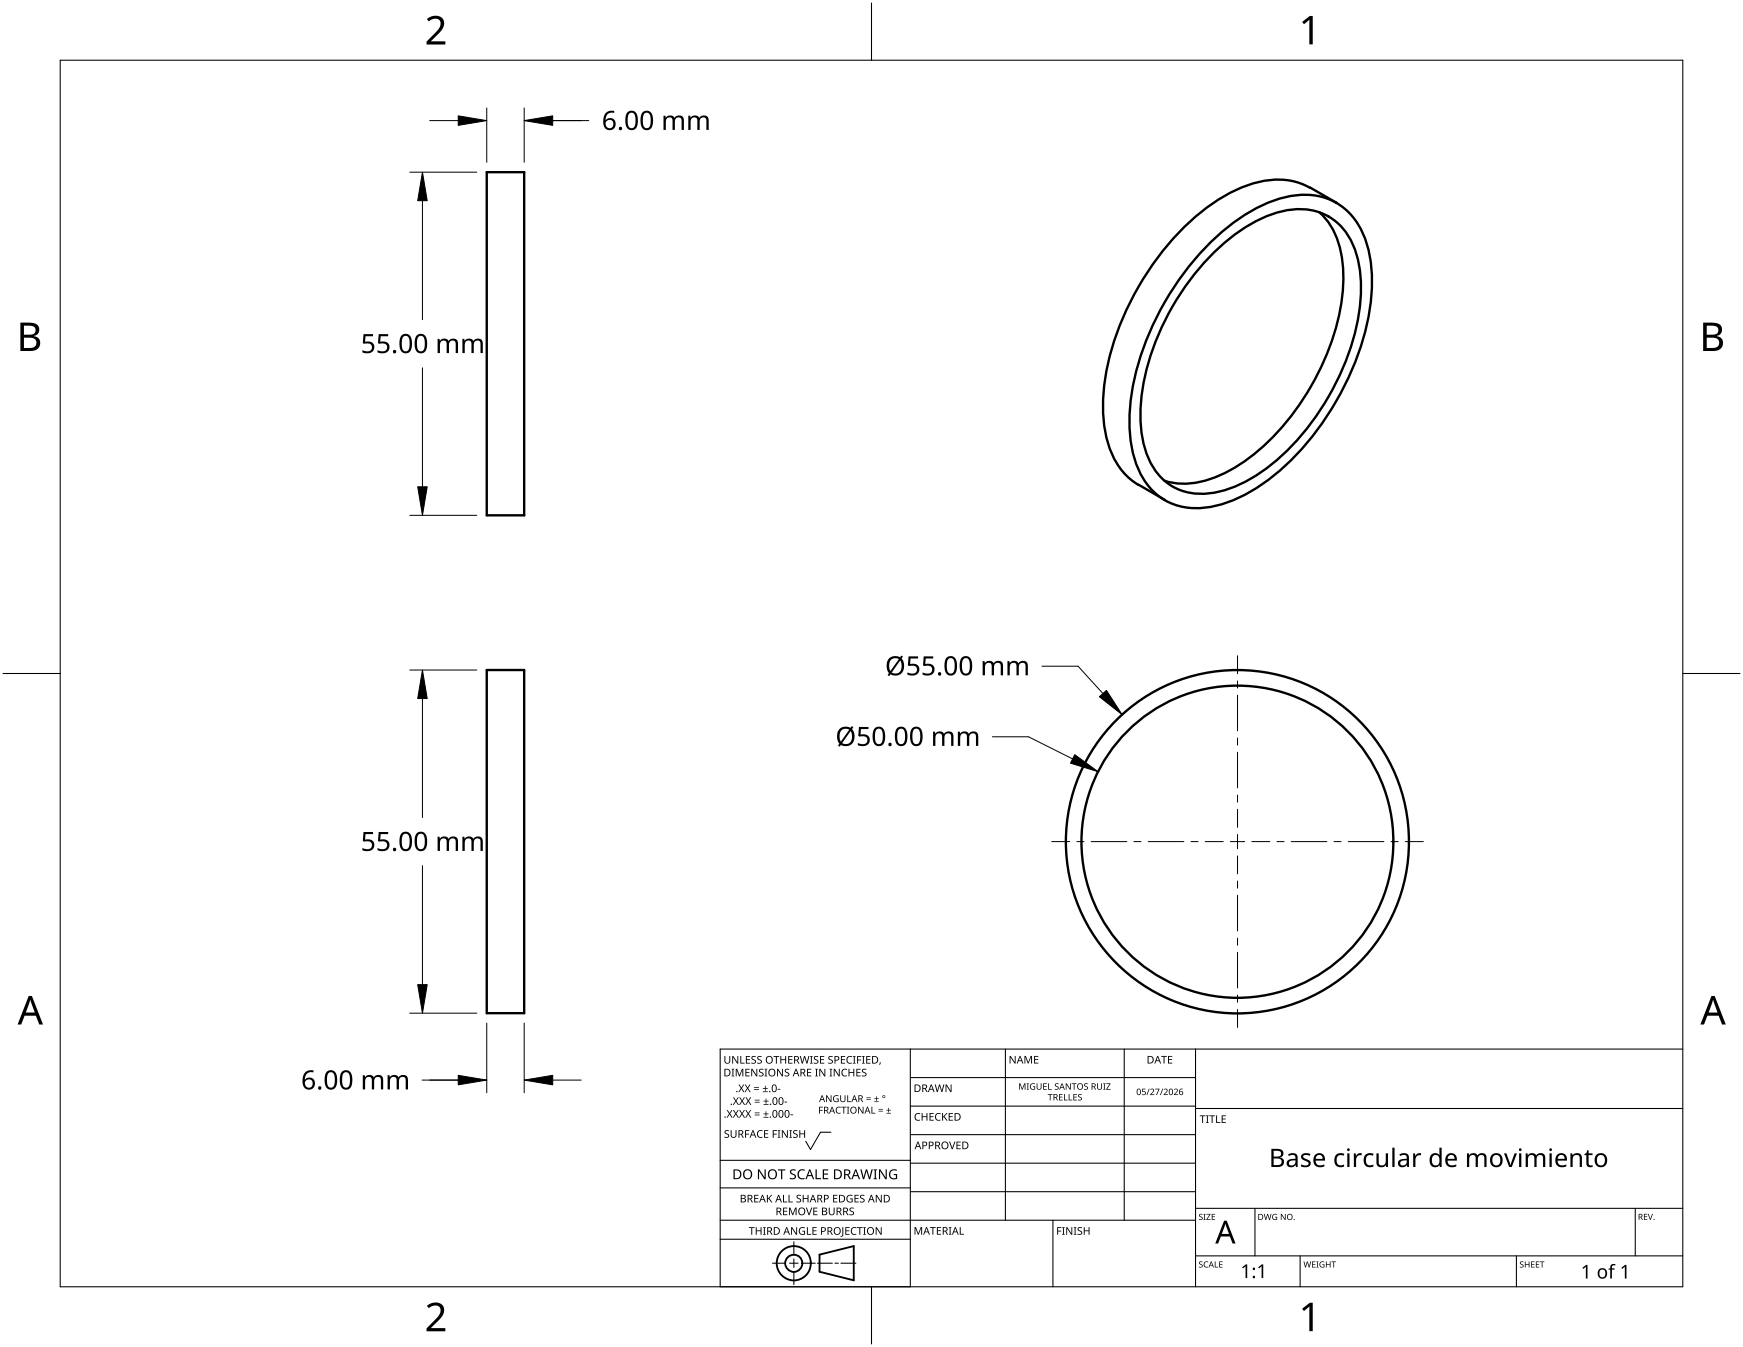
[picture p63: page 1]
