ErickHuancas/FdD_Equipo_03/Proyecto/Módulo Mecánico/V2.0/Onshape/Planos/Base de soporte para la caja V2.0.pdf

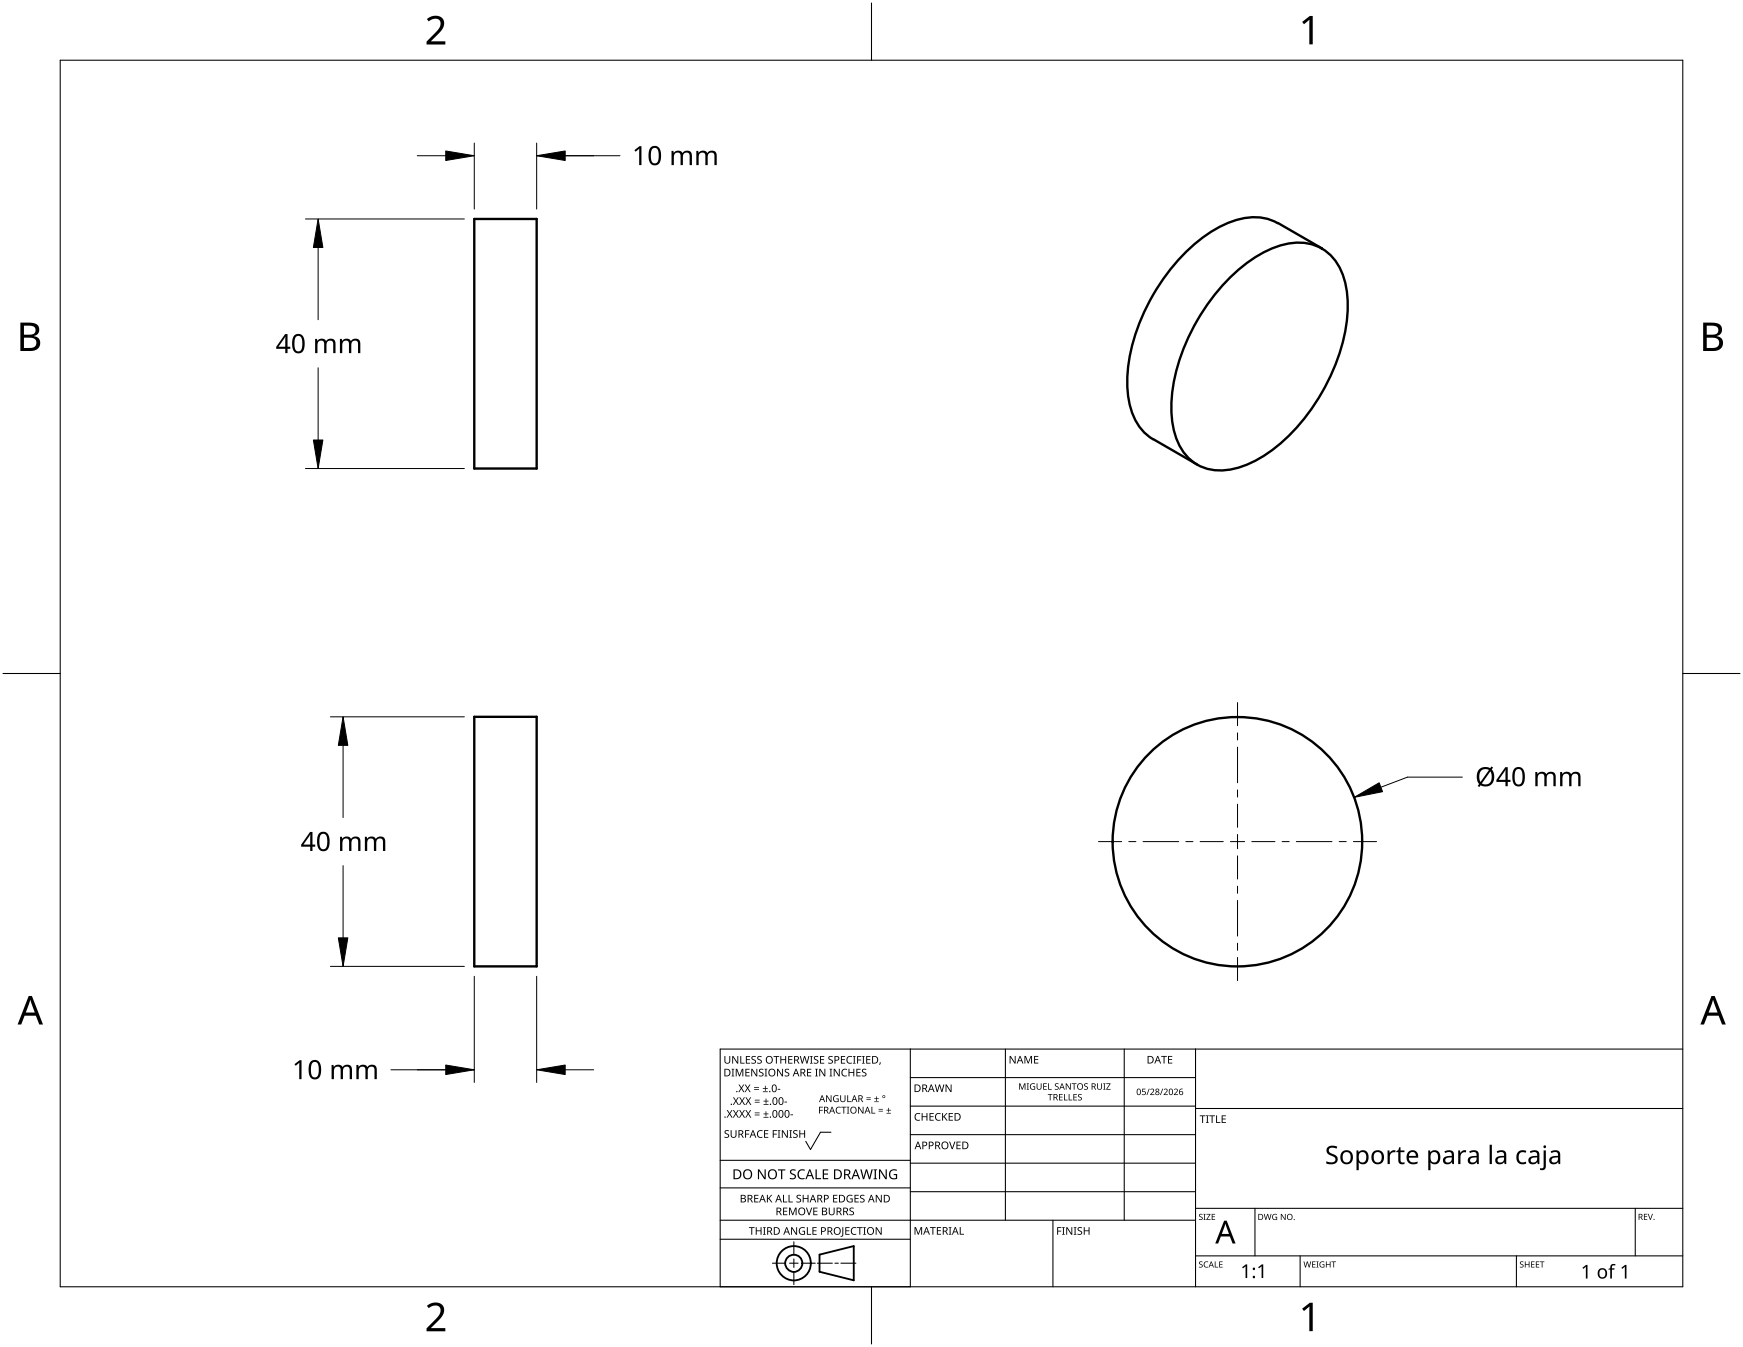
[picture p64: page 1]
