ErickHuancas/FdD_Equipo_03/Proyecto/Módulo Mecánico/V2.0/Onshape/Planos/Base para el tomate corregido V2.0.pdf

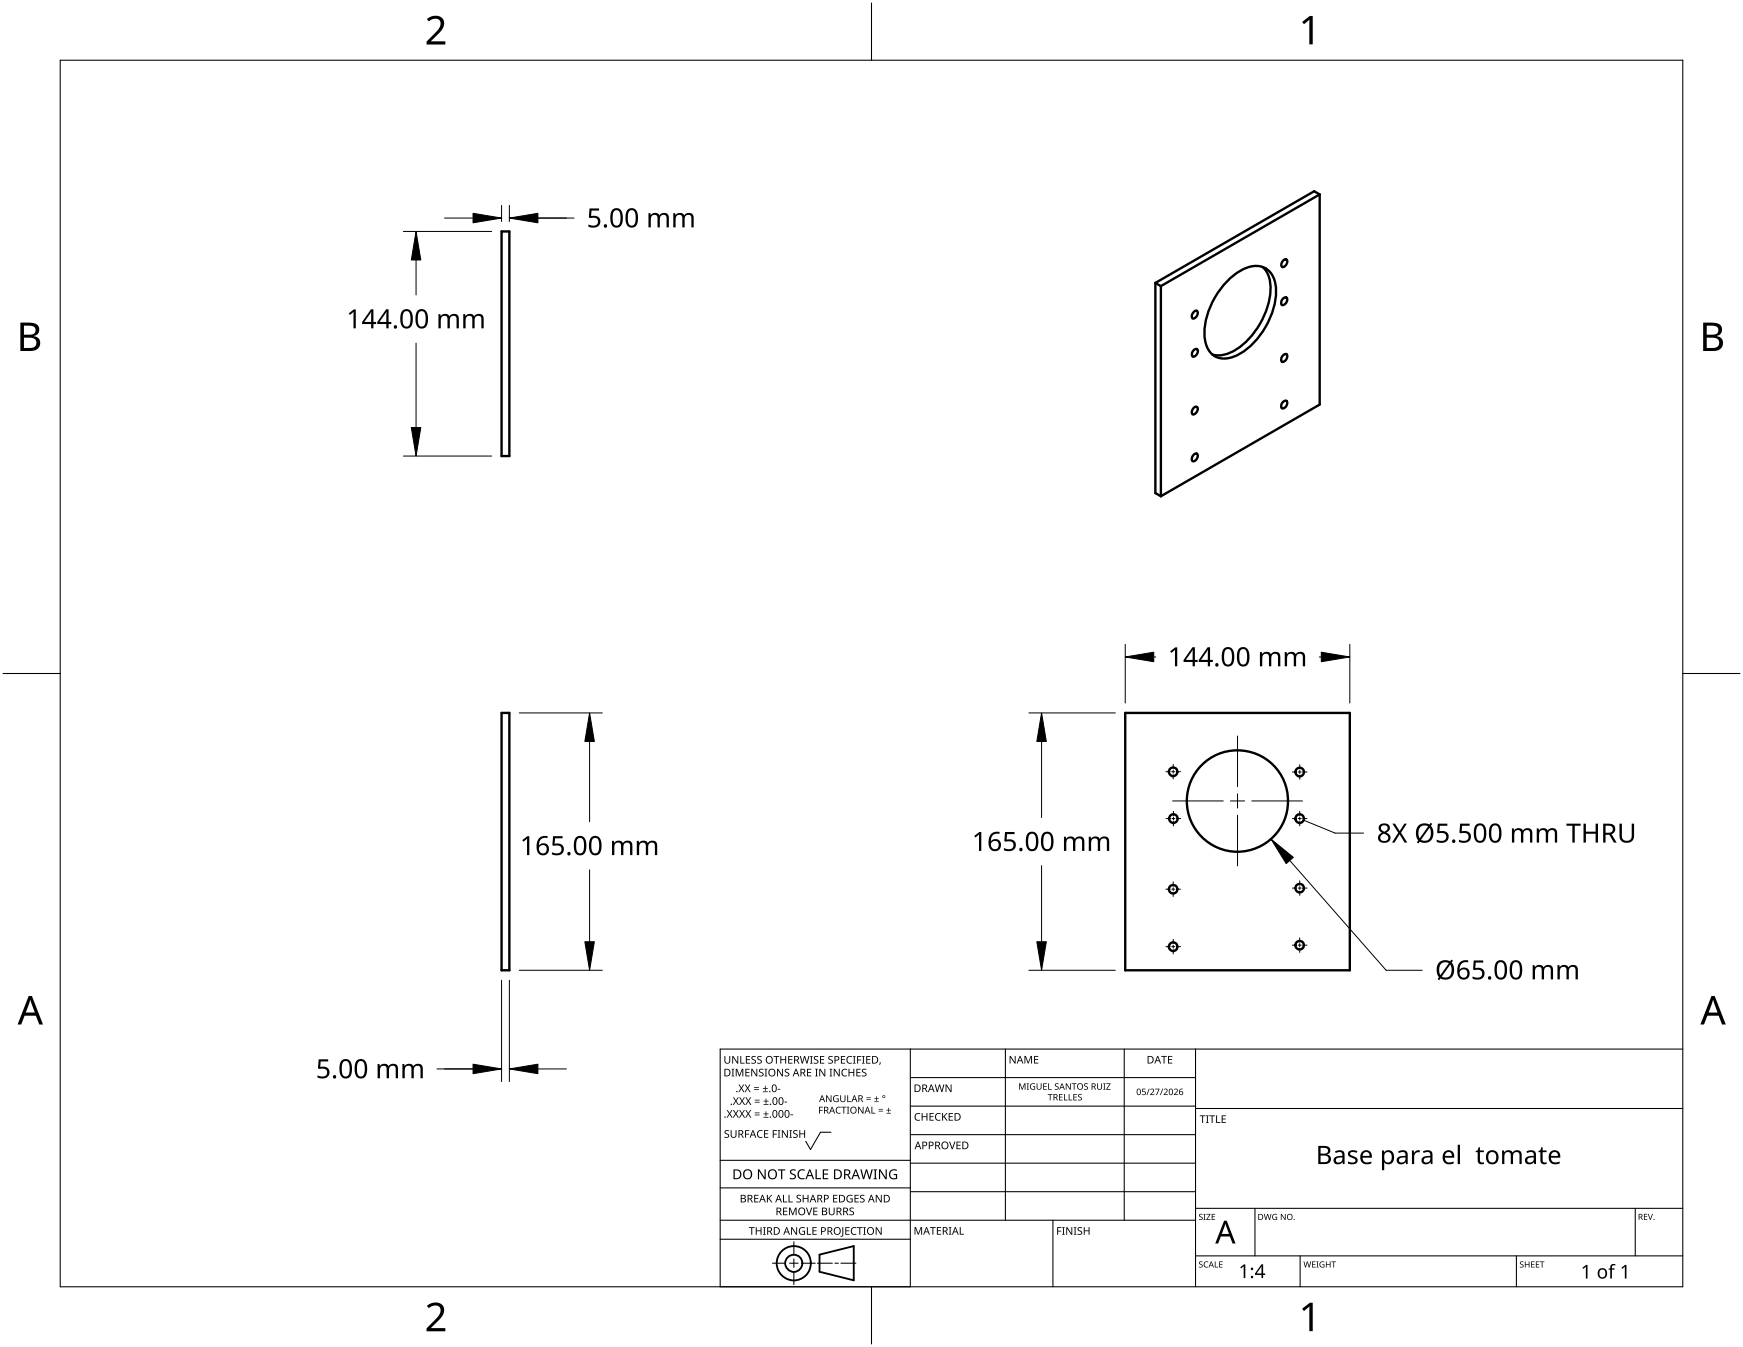
[picture p65: page 1]
