ErickHuancas/FdD_Equipo_03/Proyecto/Módulo Mecánico/V2.0/Onshape/Planos/Base para sensores corregido V2.0.pdf

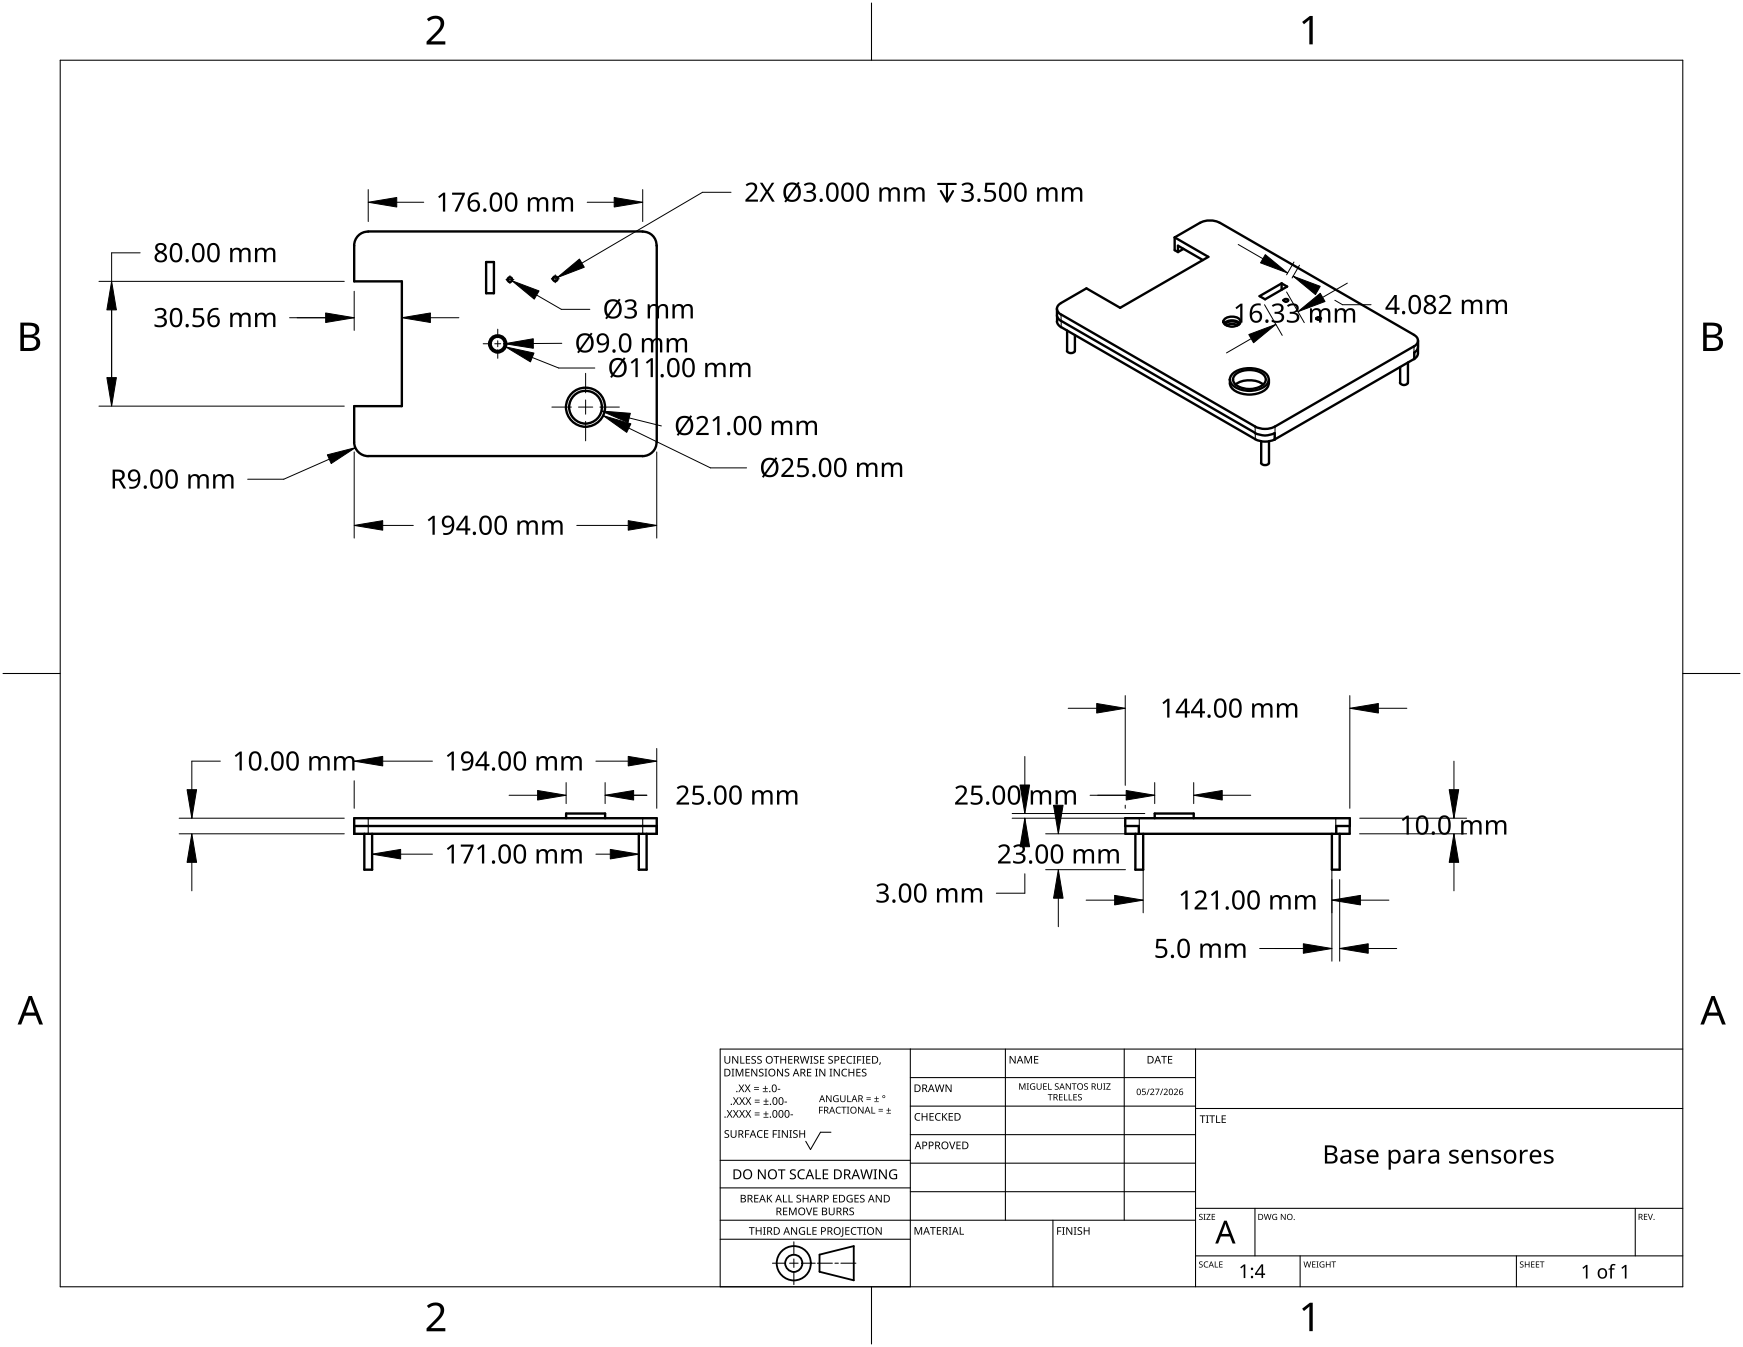
[picture p66: page 1]
