ErickHuancas/FdD_Equipo_03/Proyecto/Módulo Mecánico/V2.0/Onshape/Planos/Caja fresh TOMATE corregido V2.0.pdf

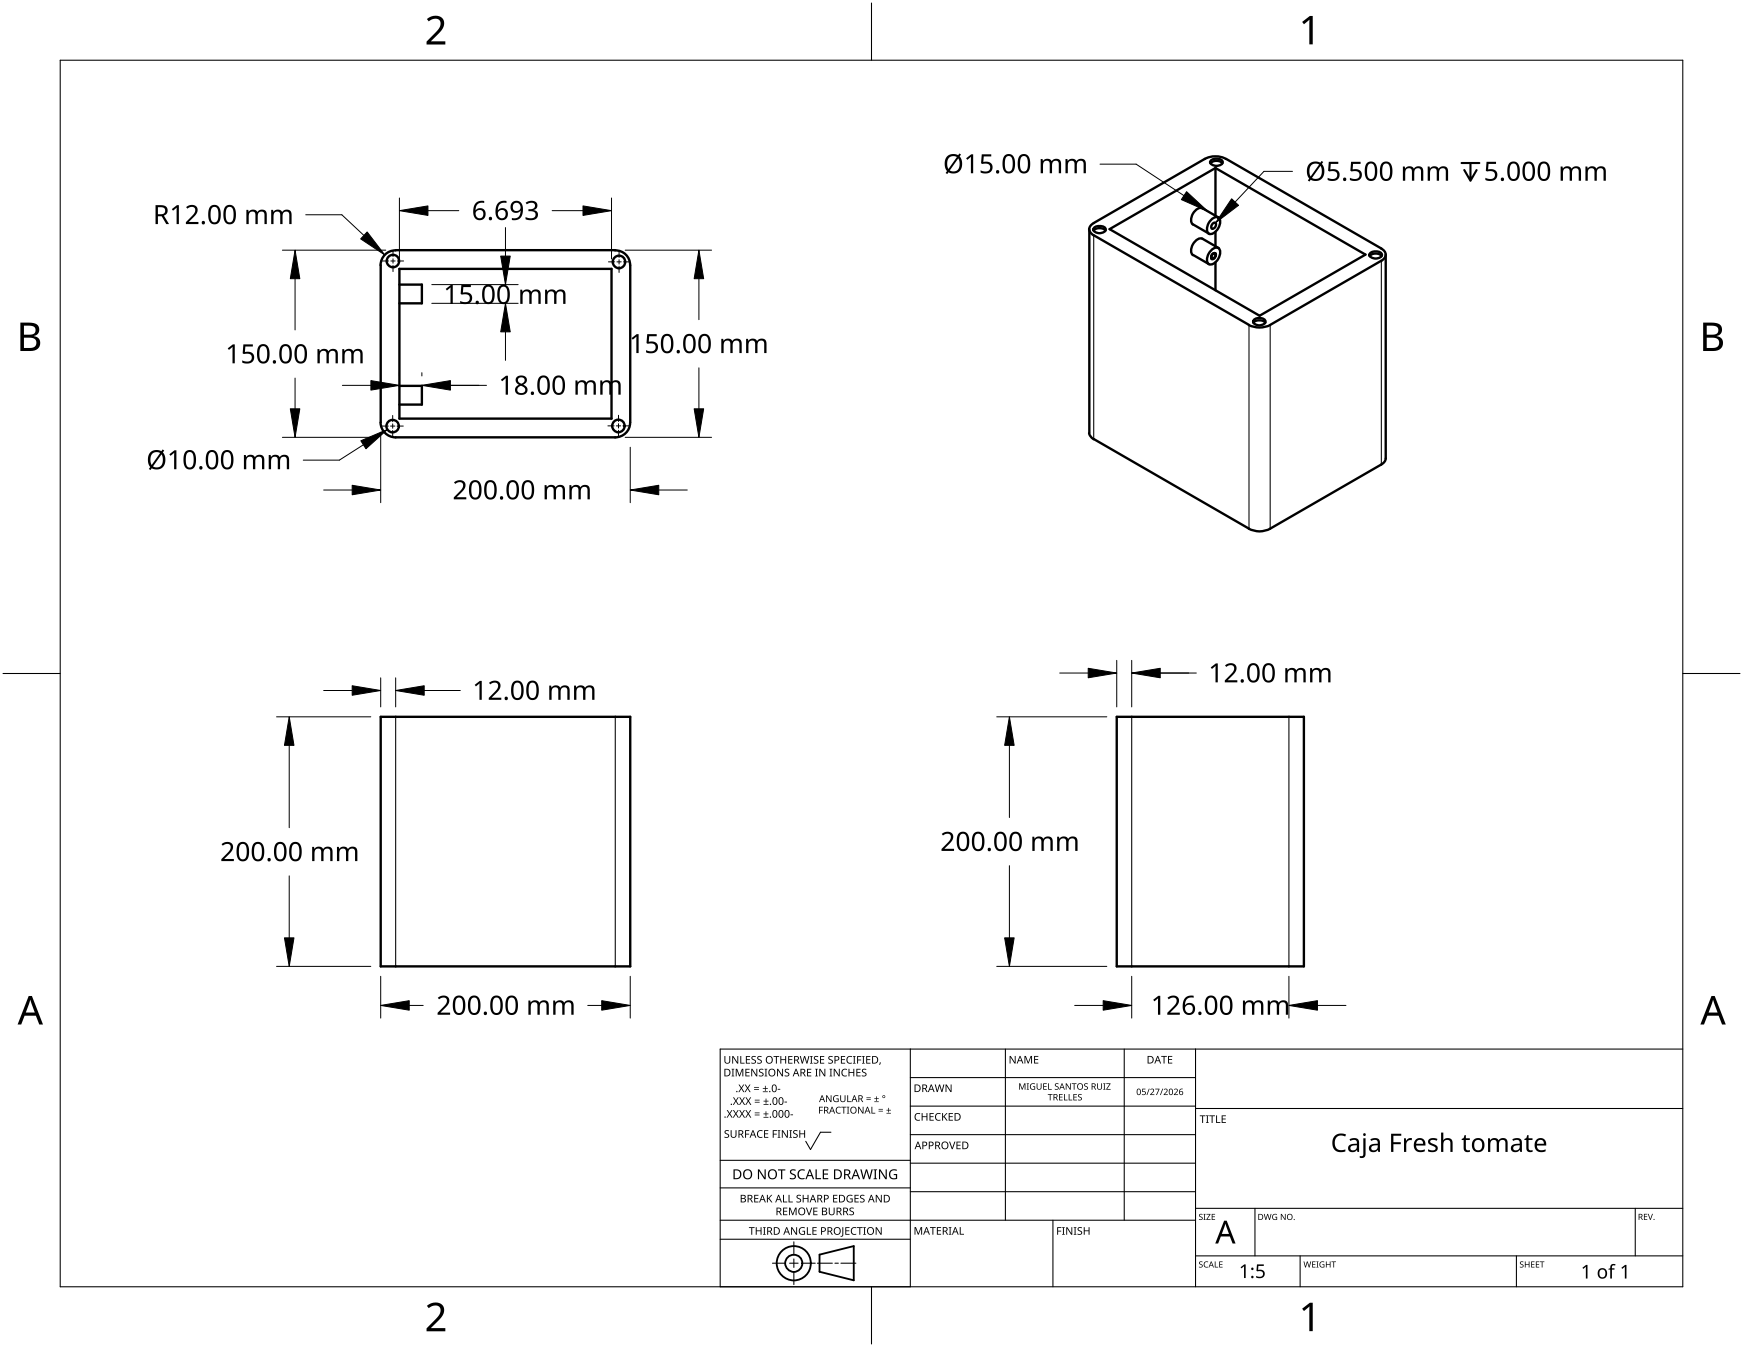
[picture p67: page 1]
