ErickHuancas/FdD_Equipo_03/Proyecto/Módulo Mecánico/V2.0/Onshape/Planos/Tapa delantera corregido V2.0.pdf

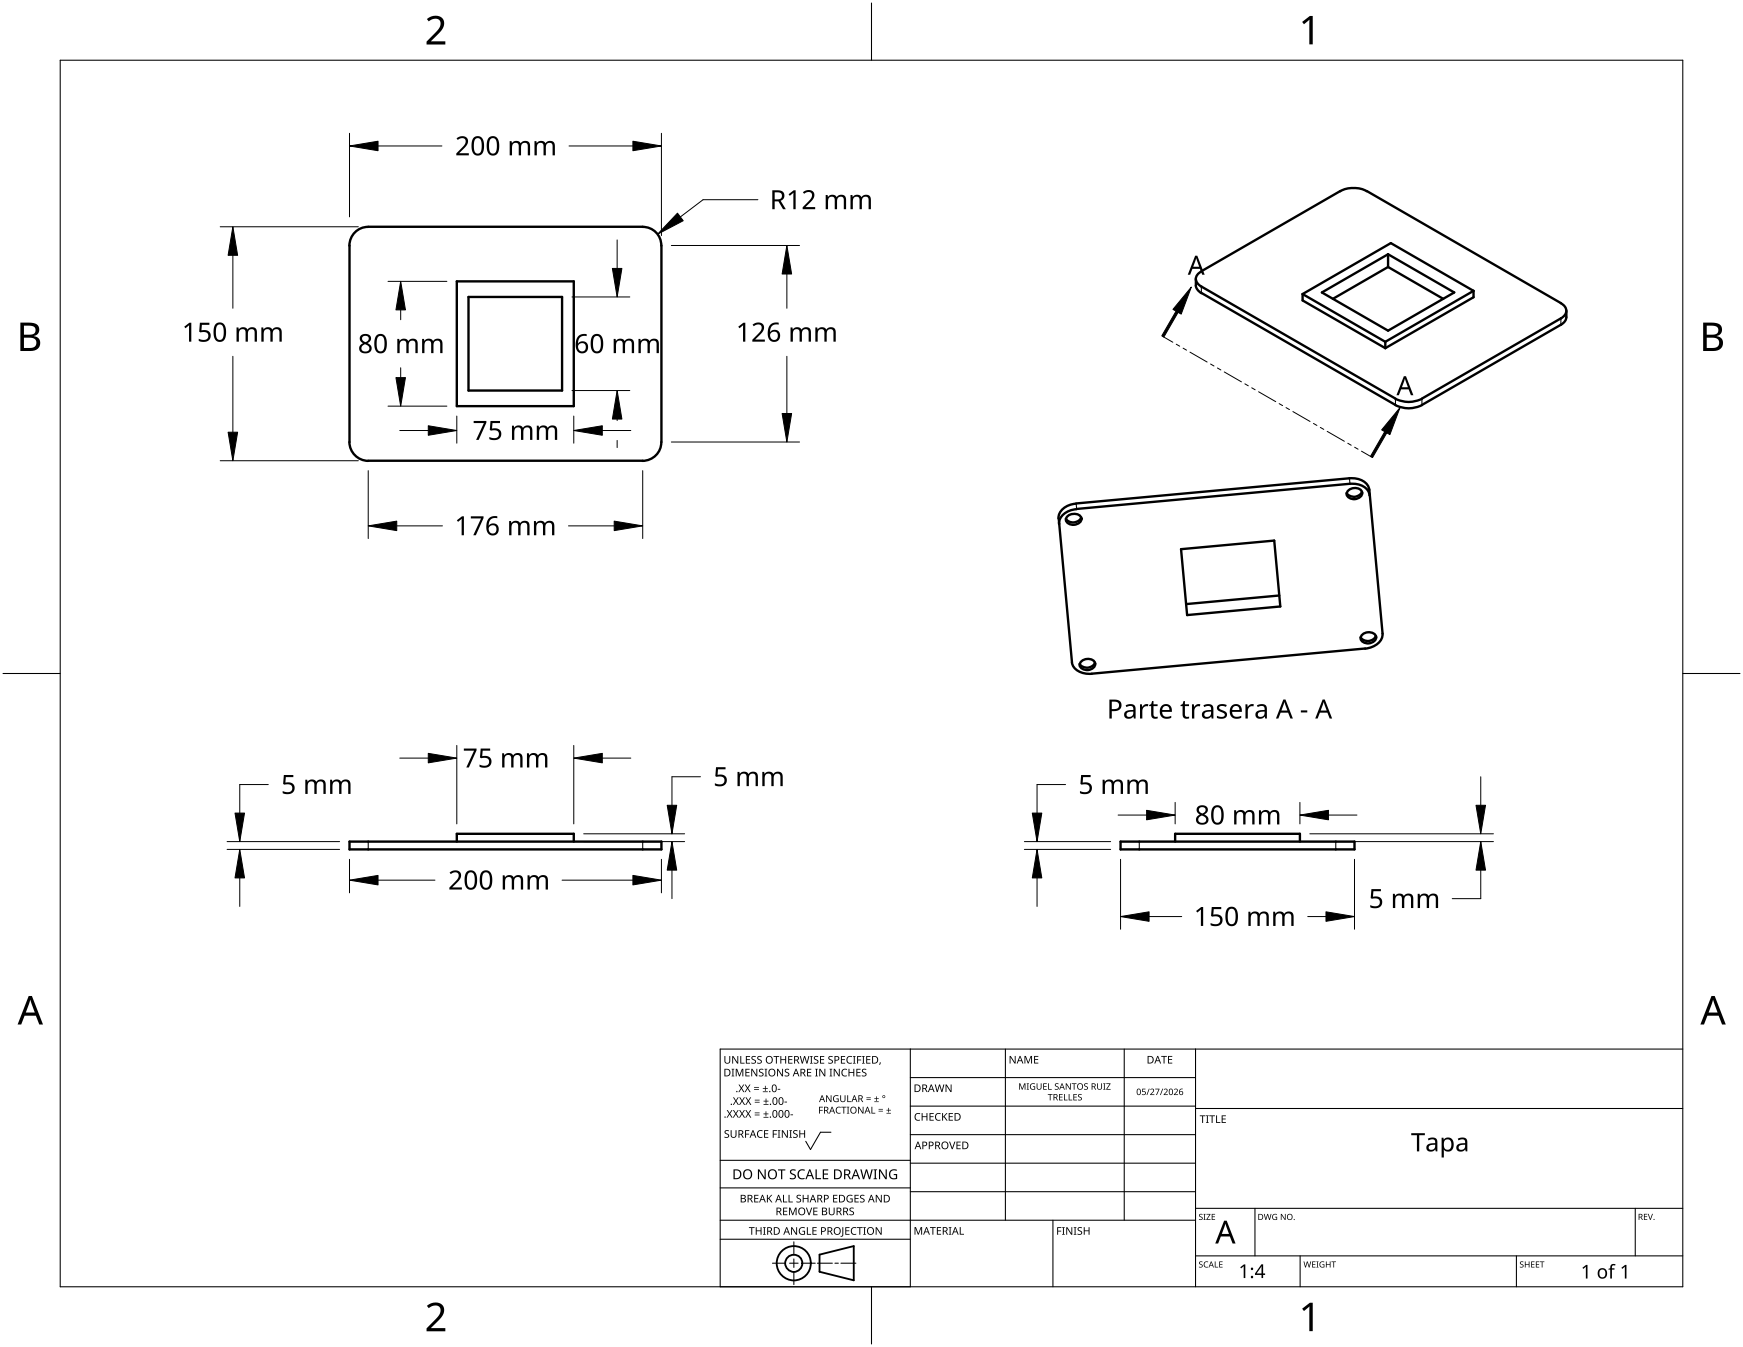
[picture p68: page 1]
