ErickHuancas/FdD_Equipo_03/Proyecto/Módulo Mecánico/V2.0/Onshape/Planos/Tapa trasera corregido V2.0.pdf

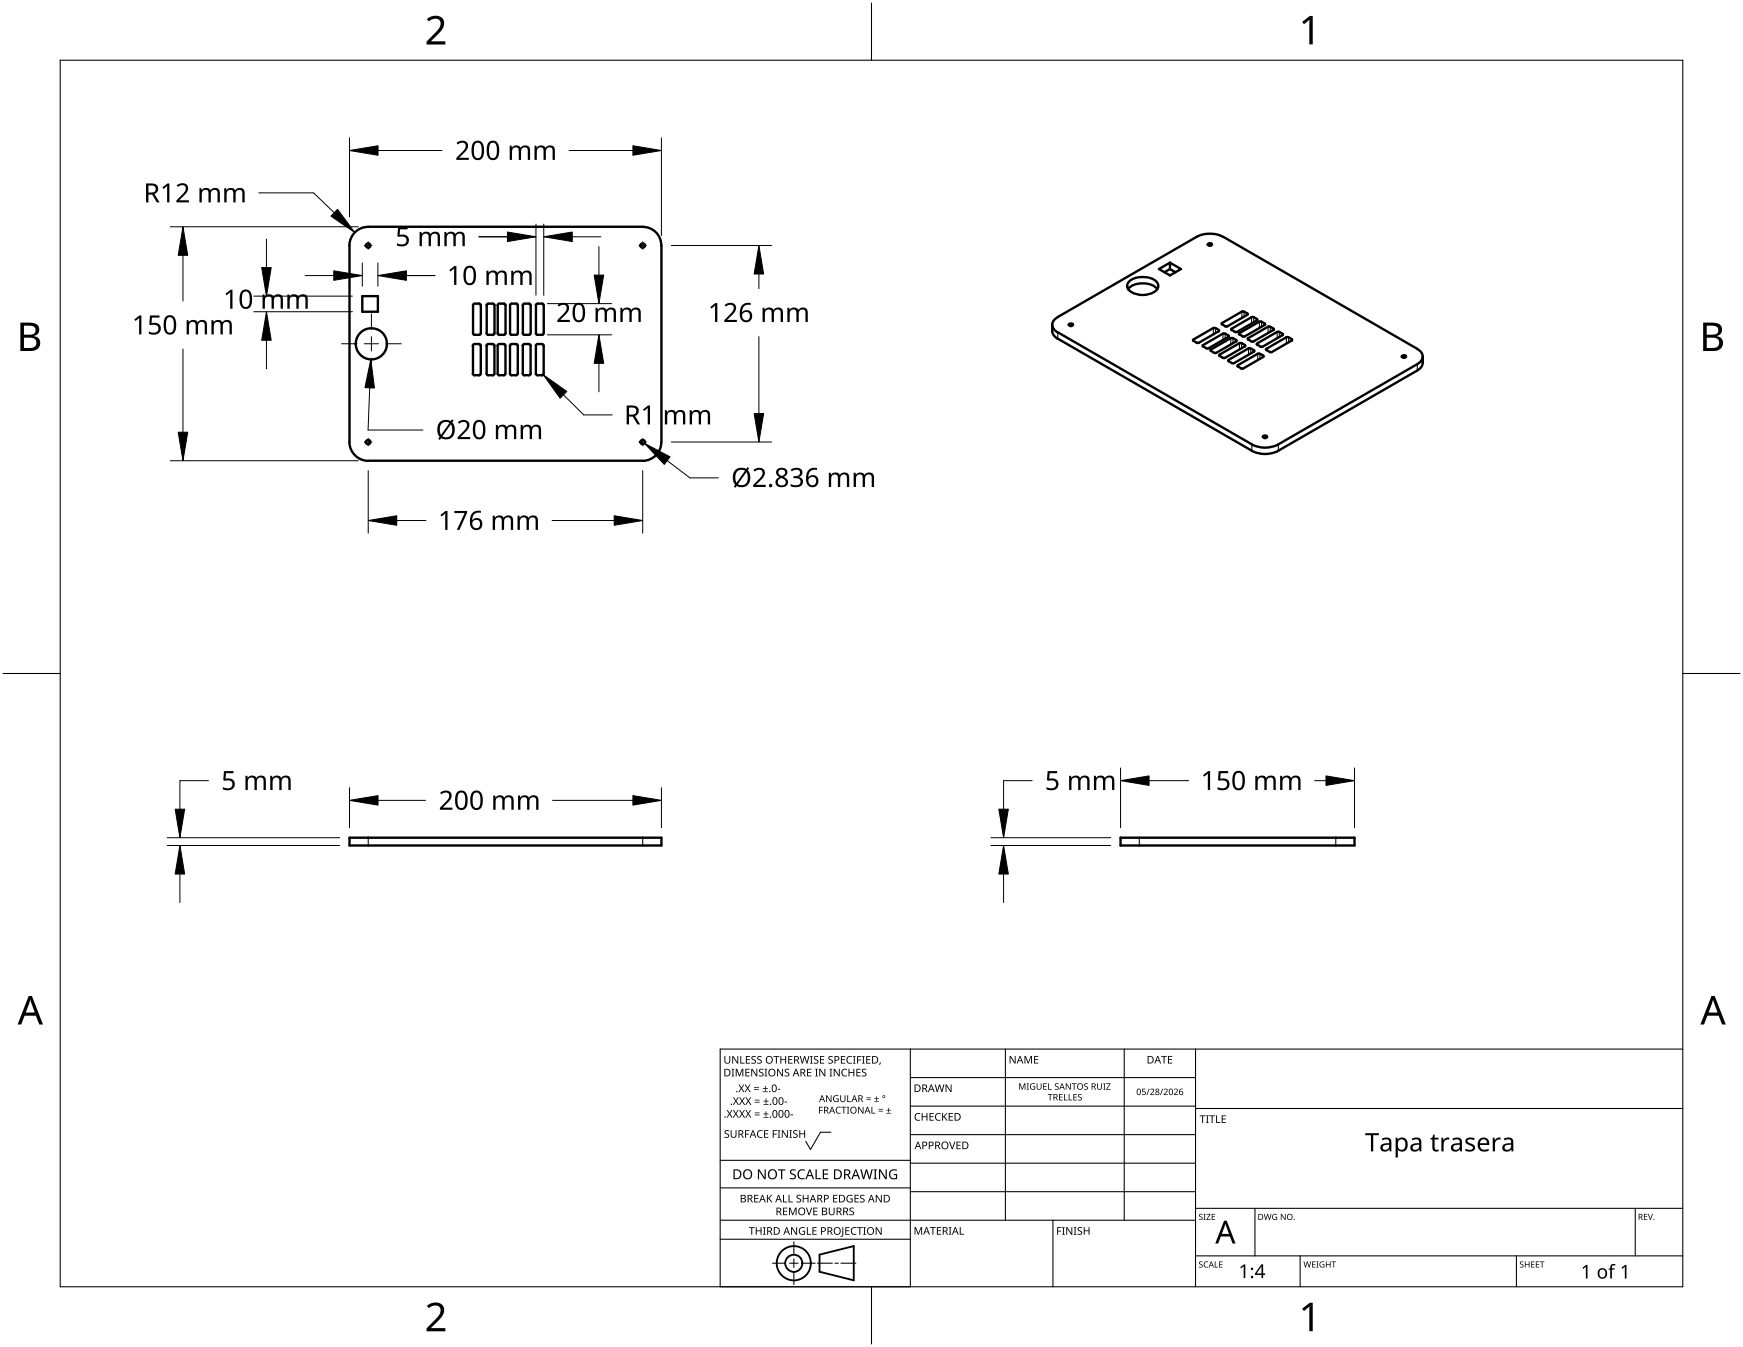
[picture p69: page 1]
