ErickHuancas/FdD_Equipo_03/Proyecto/Módulo Mecánico/V1.0/Onshape/Planos/Bases de soporte de la caja-Fresh Tomato V1.0.pdf

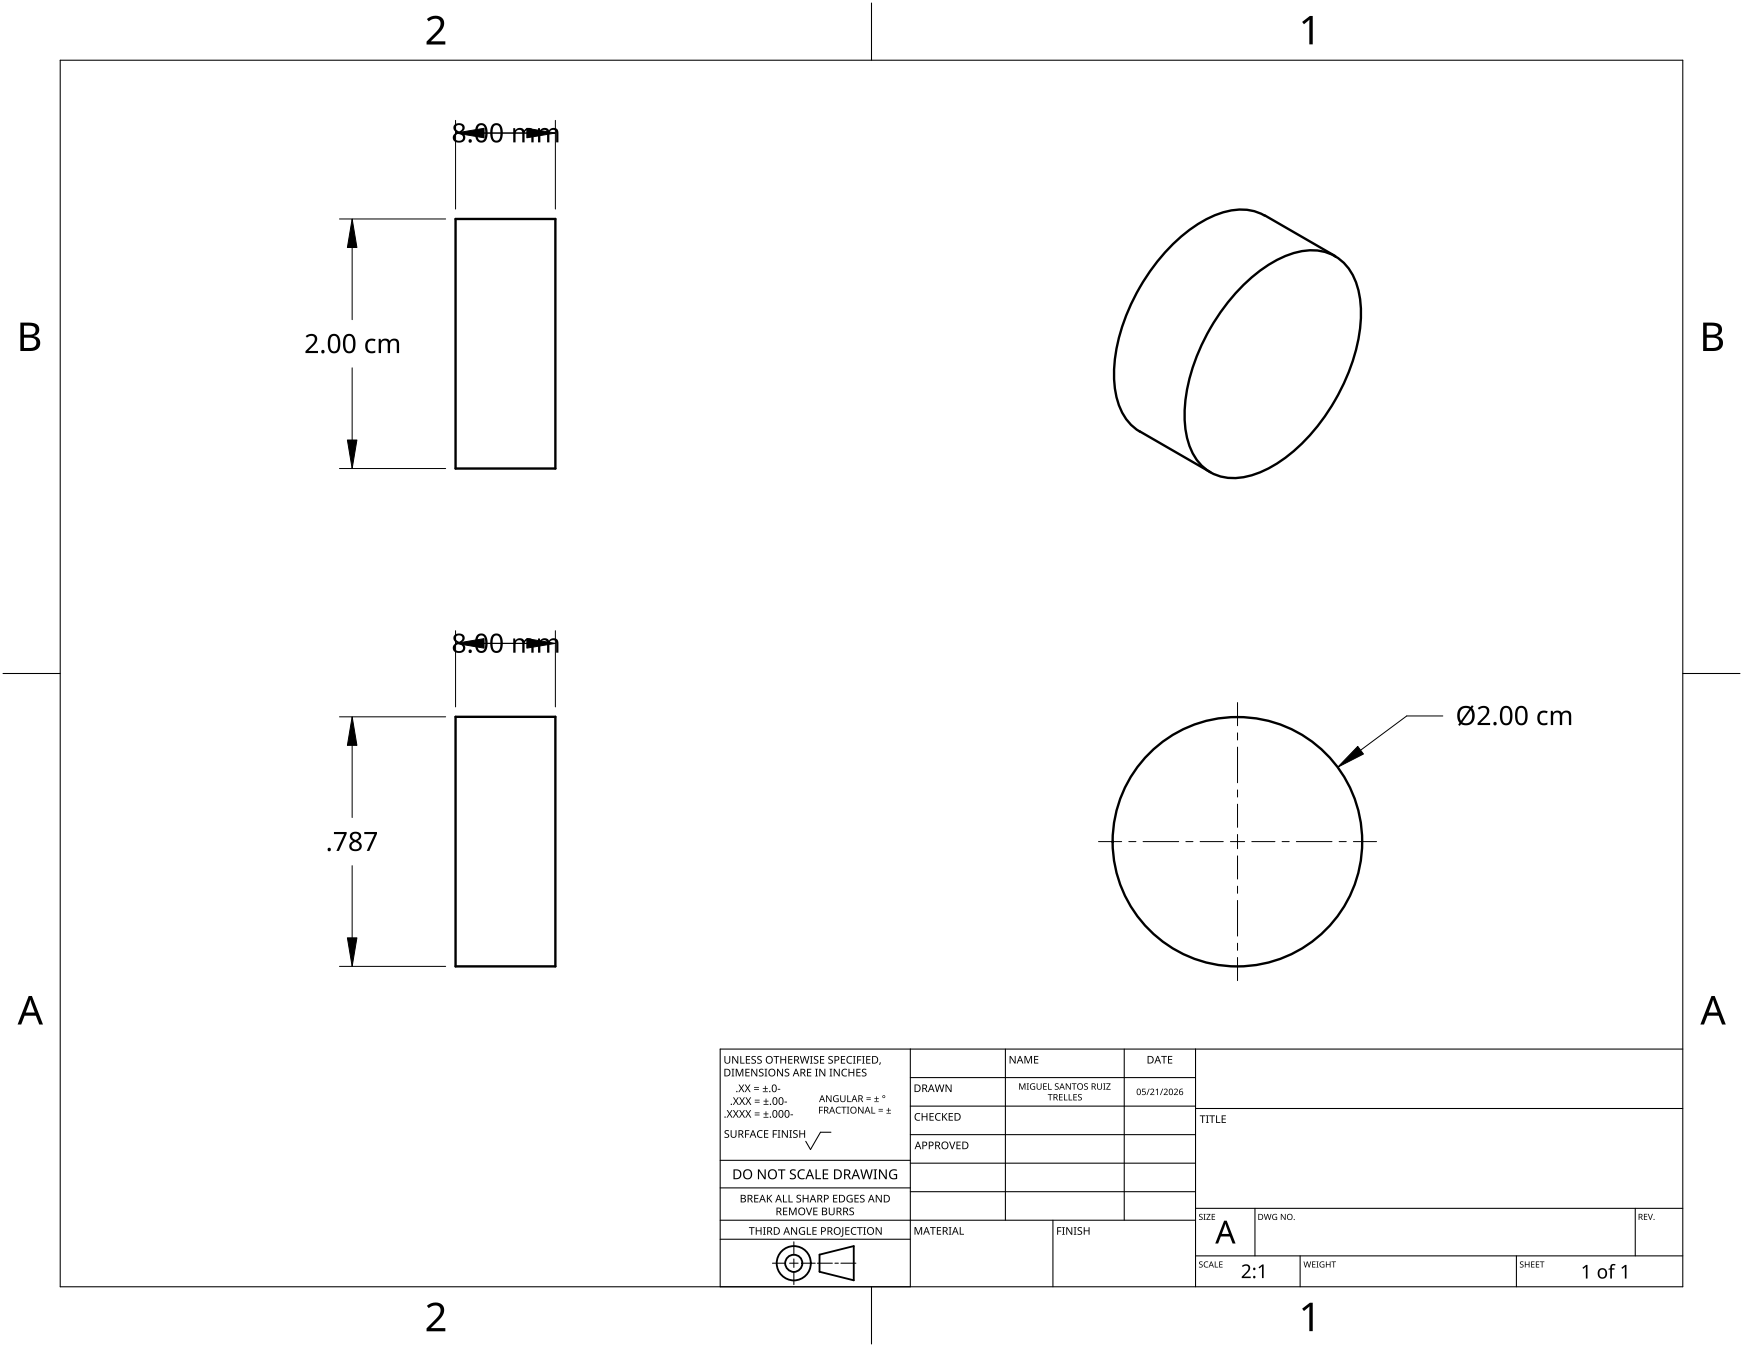
[picture p70: page 1]
