ErickHuancas/FdD_Equipo_03/Proyecto/Módulo Mecánico/V1.0/Onshape/Planos/Base de sensores V1.0.pdf

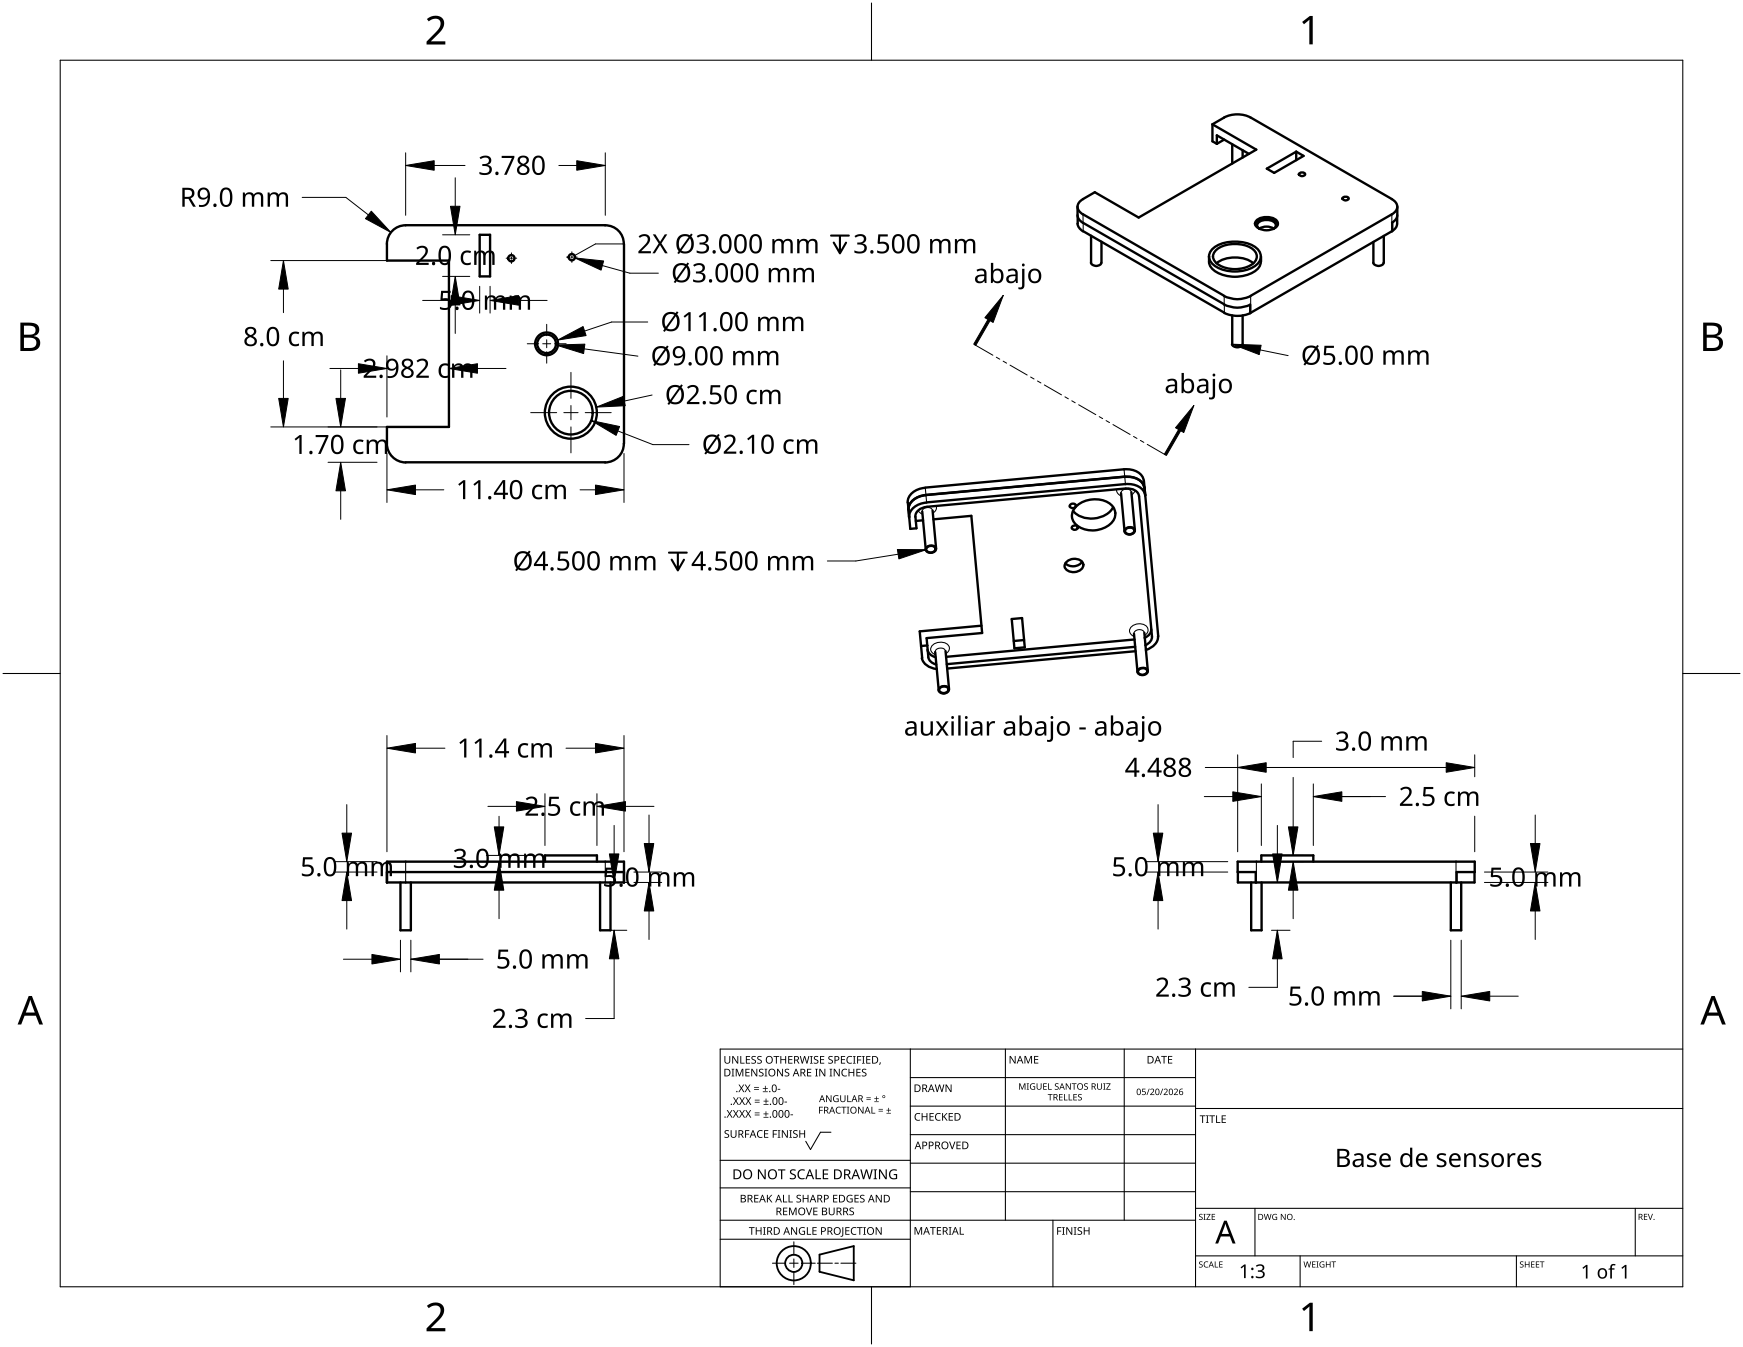
[picture p71: page 1]
