ErickHuancas/FdD_Equipo_03/Proyecto/Módulo Mecánico/V1.0/Onshape/Planos/Base de tomate V1.0.pdf

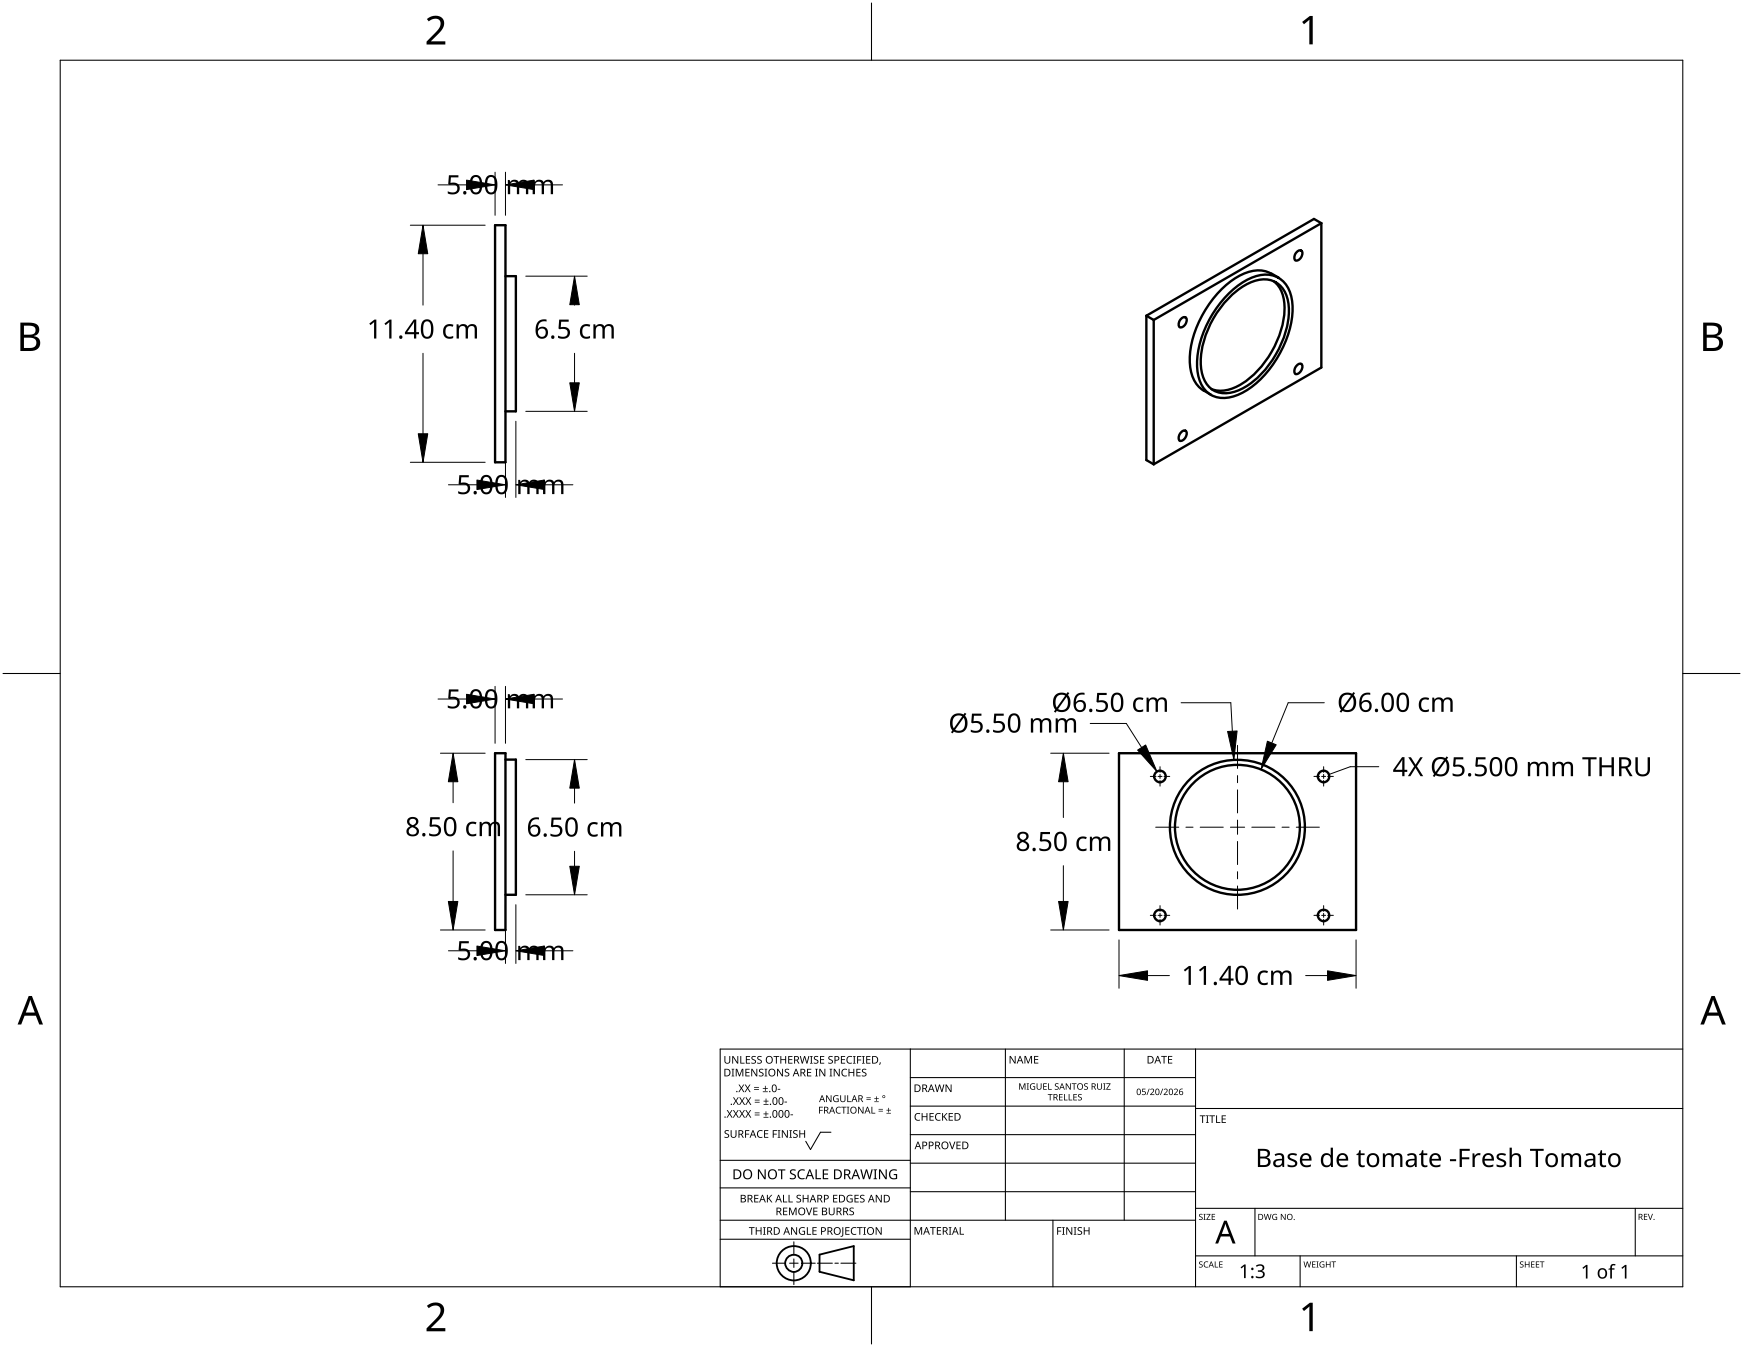
[picture p72: page 1]
