ErickHuancas/FdD_Equipo_03/Proyecto/Módulo Mecánico/V1.0/Onshape/Planos/Contorno de Fresh tomato V1.0.pdf

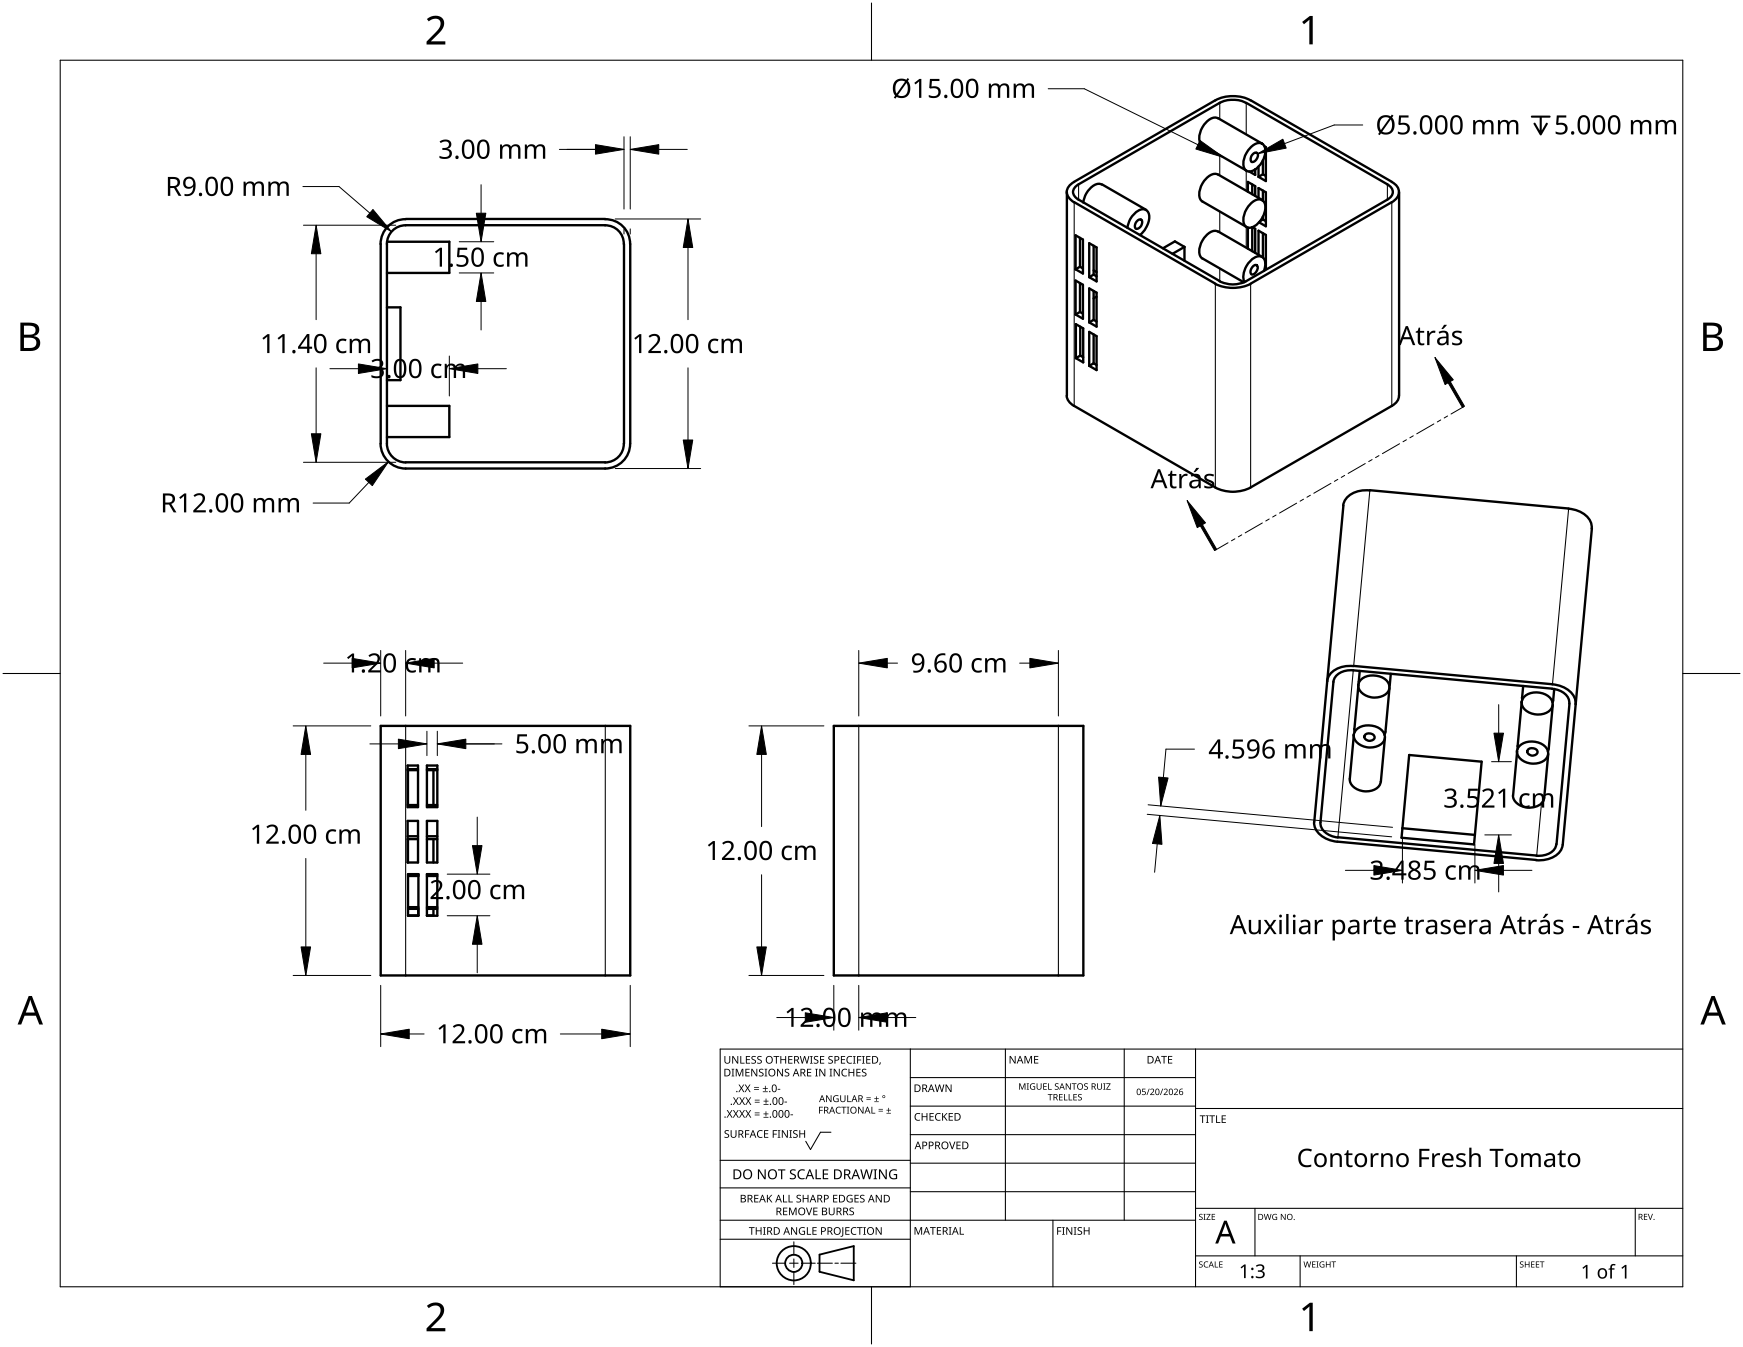
[picture p73: page 1]
