ErickHuancas/FdD_Equipo_03/Proyecto/Módulo Mecánico/V1.0/Onshape/Planos/Tapa delantera V1.0.pdf

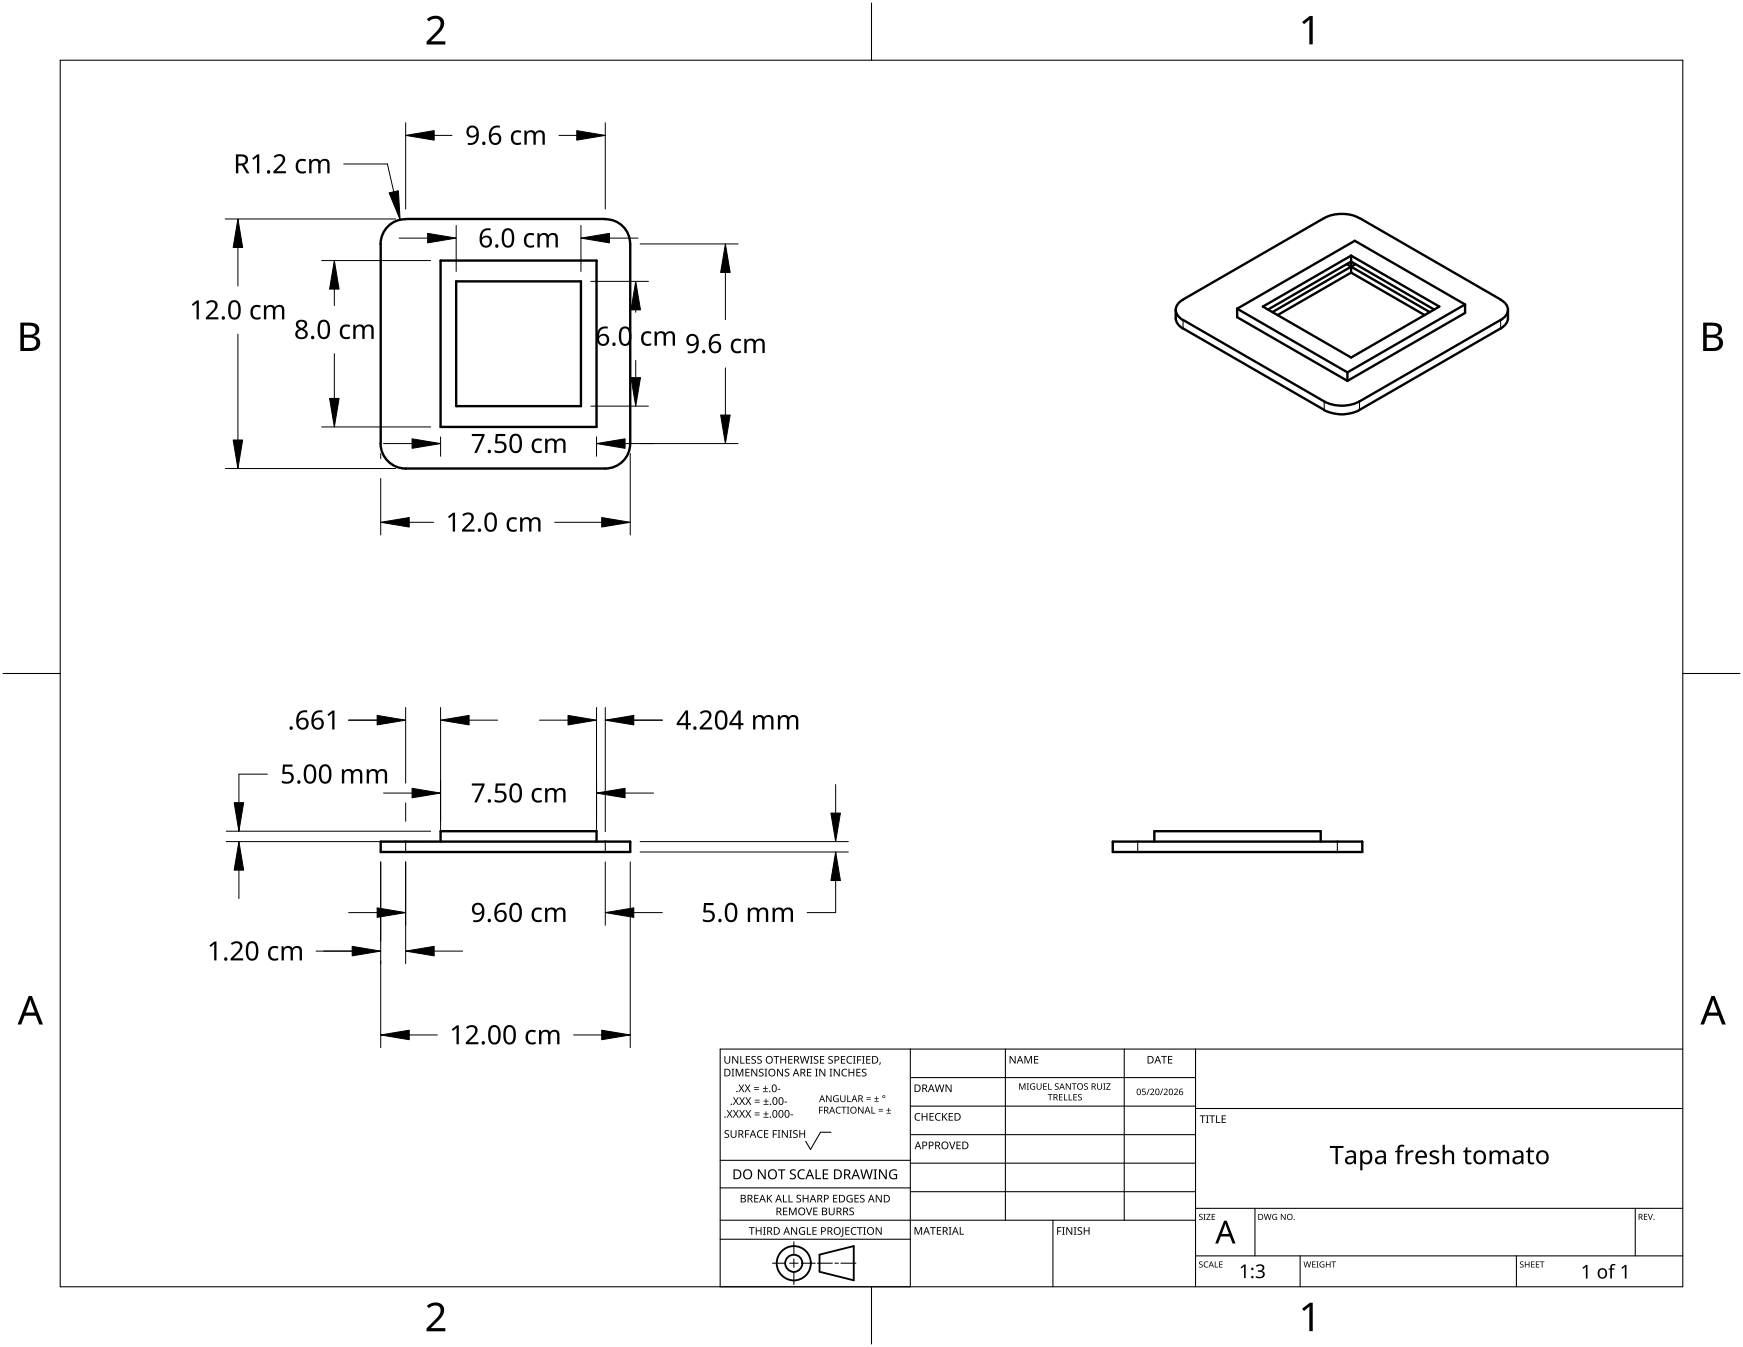
[picture p74: page 1]
