ErickHuancas/FdD_Equipo_03/Proyecto/Módulo Mecánico/V1.0/Onshape/Planos/Tapa trasera V1.0.pdf

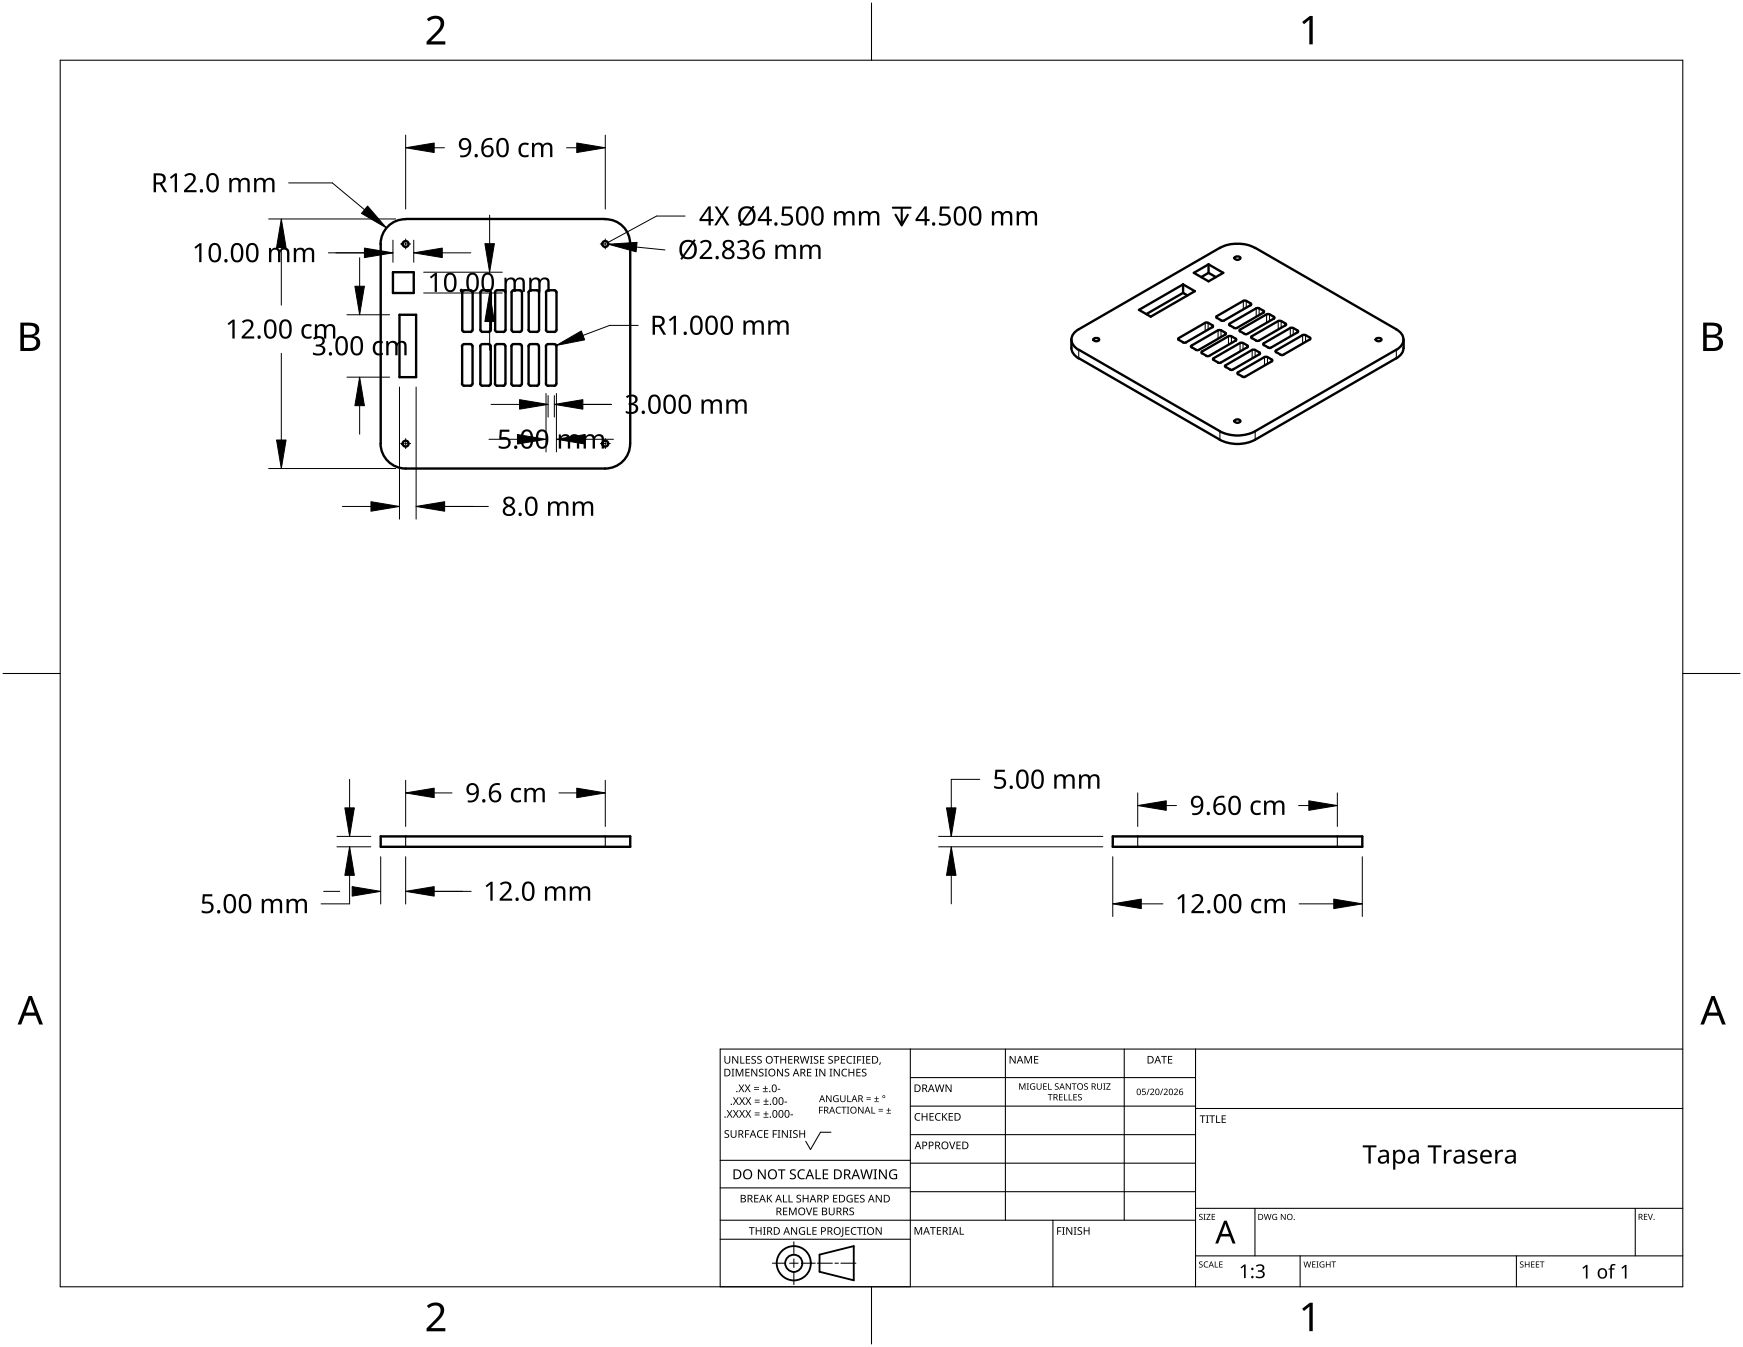
[picture p75: page 1]
